andykarpov/PiRadio-20x4LCD/schematic/build/pdf/volume_v_1_0_pcb_top.pdf

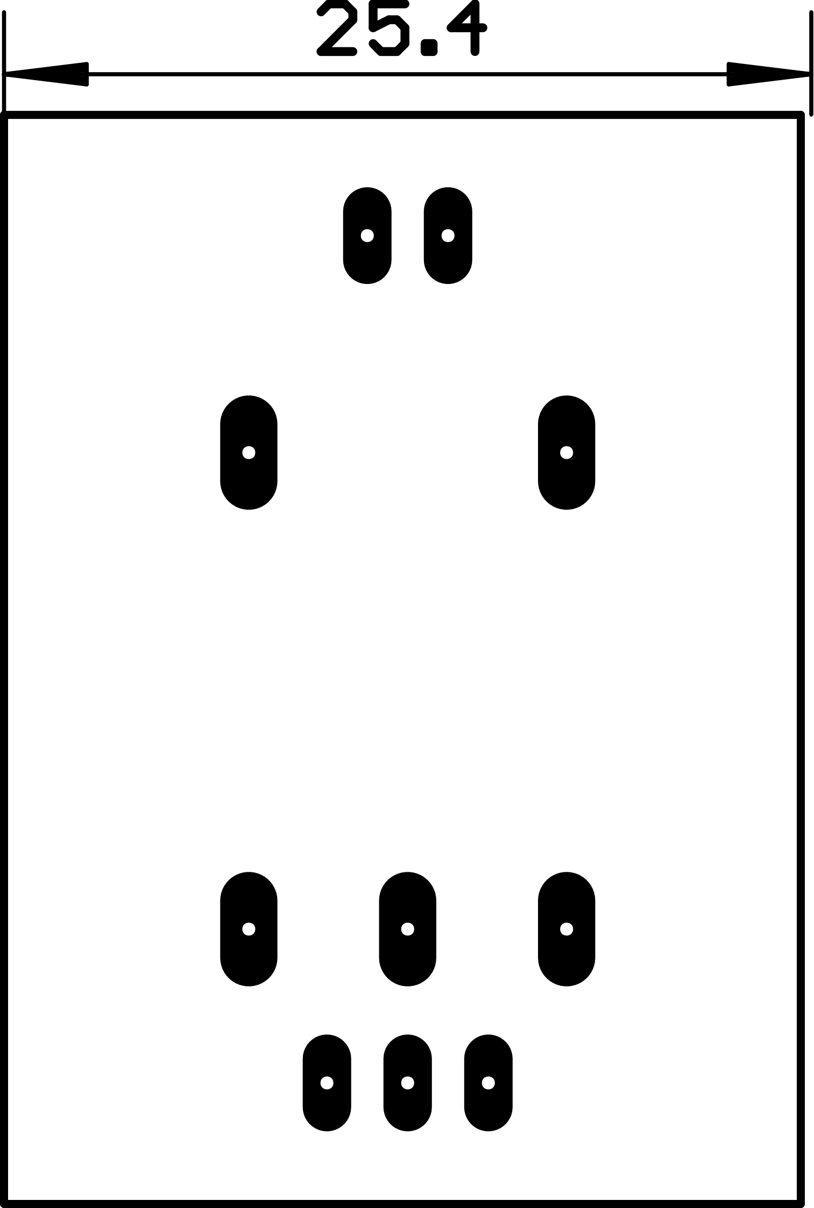
[picture p1: figure]
