andykarpov/PiRadio-20x4LCD/schematic/build/png/encoder_v_1_0_pcb_top.png

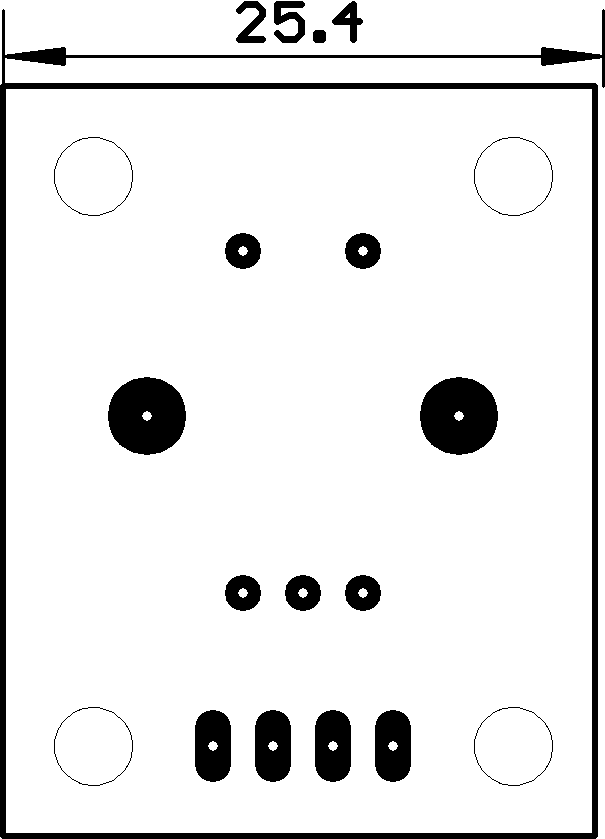
schematic/build/png/encoder_v_1_0_pcb_top.png
