andykarpov/PiRadio-20x4LCD/schematic/build/png/interface_v_1_0_pcb_bottom_vertical.png

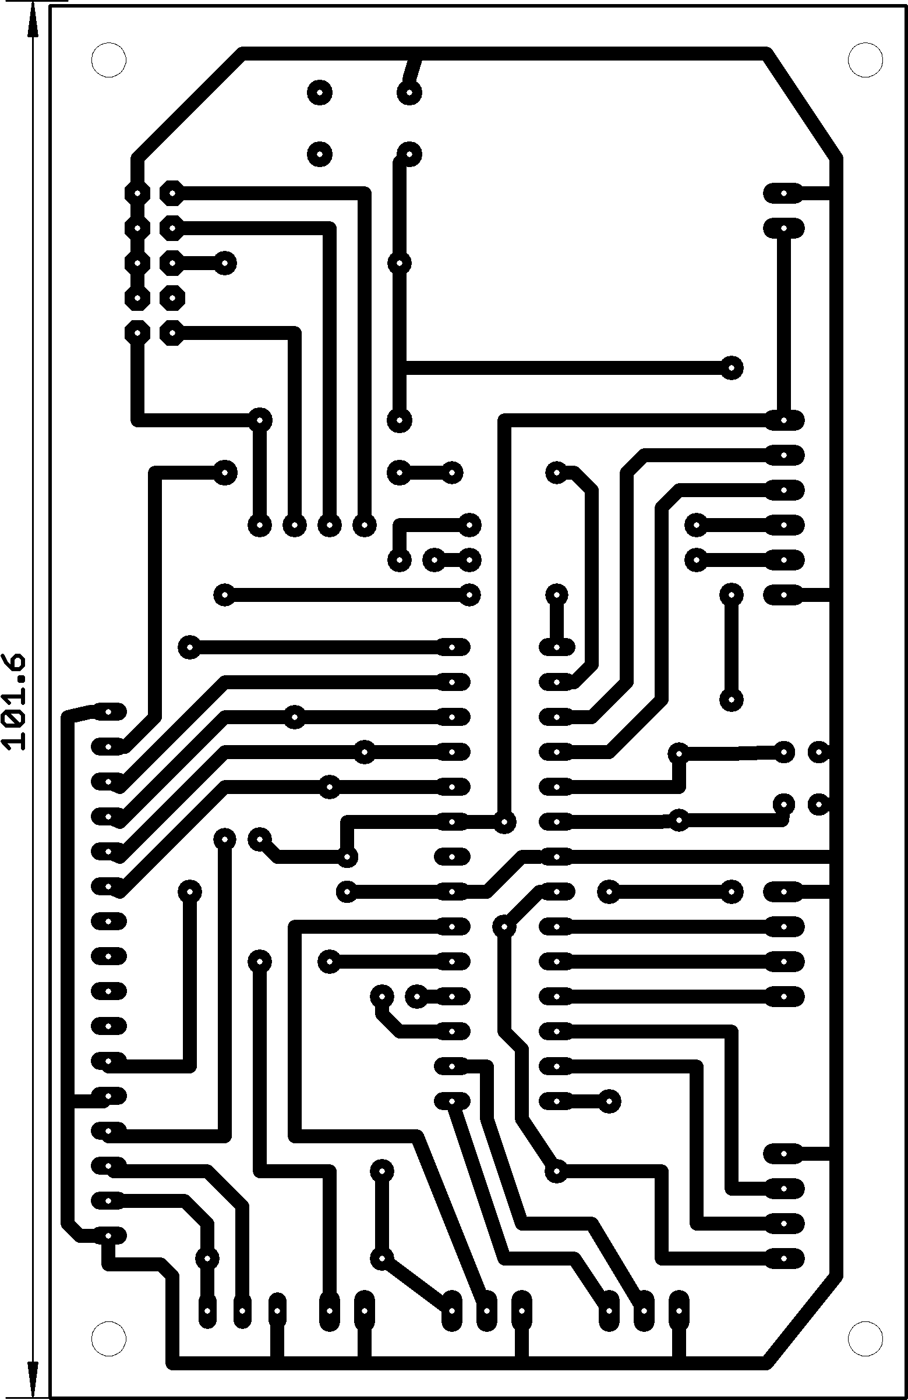
schematic/build/png/interface_v_1_0_pcb_bottom_vertical.png
