andykarpov/PiRadio-20x4LCD/schematic/build/png/pt2322_v_1_0_pcb_top_mirror.png

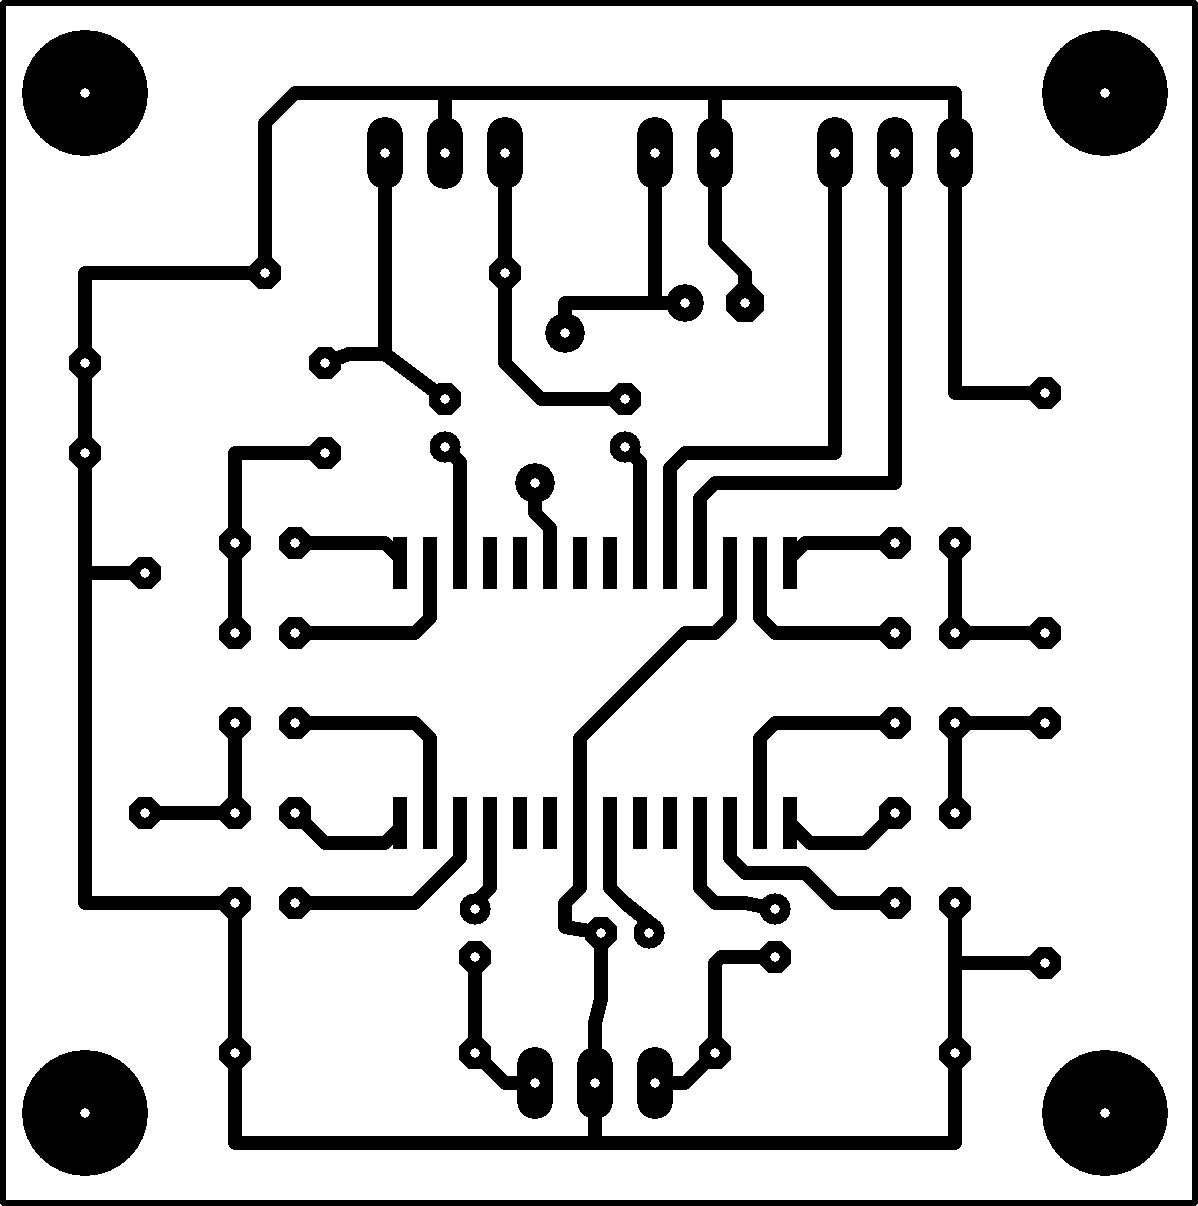
schematic/build/png/pt2322_v_1_0_pcb_top_mirror.png
