andykarpov/PiRadio-20x4LCD/schematic/build/png/tda8425_v_1_0_pcb_cmp_jumpered.png

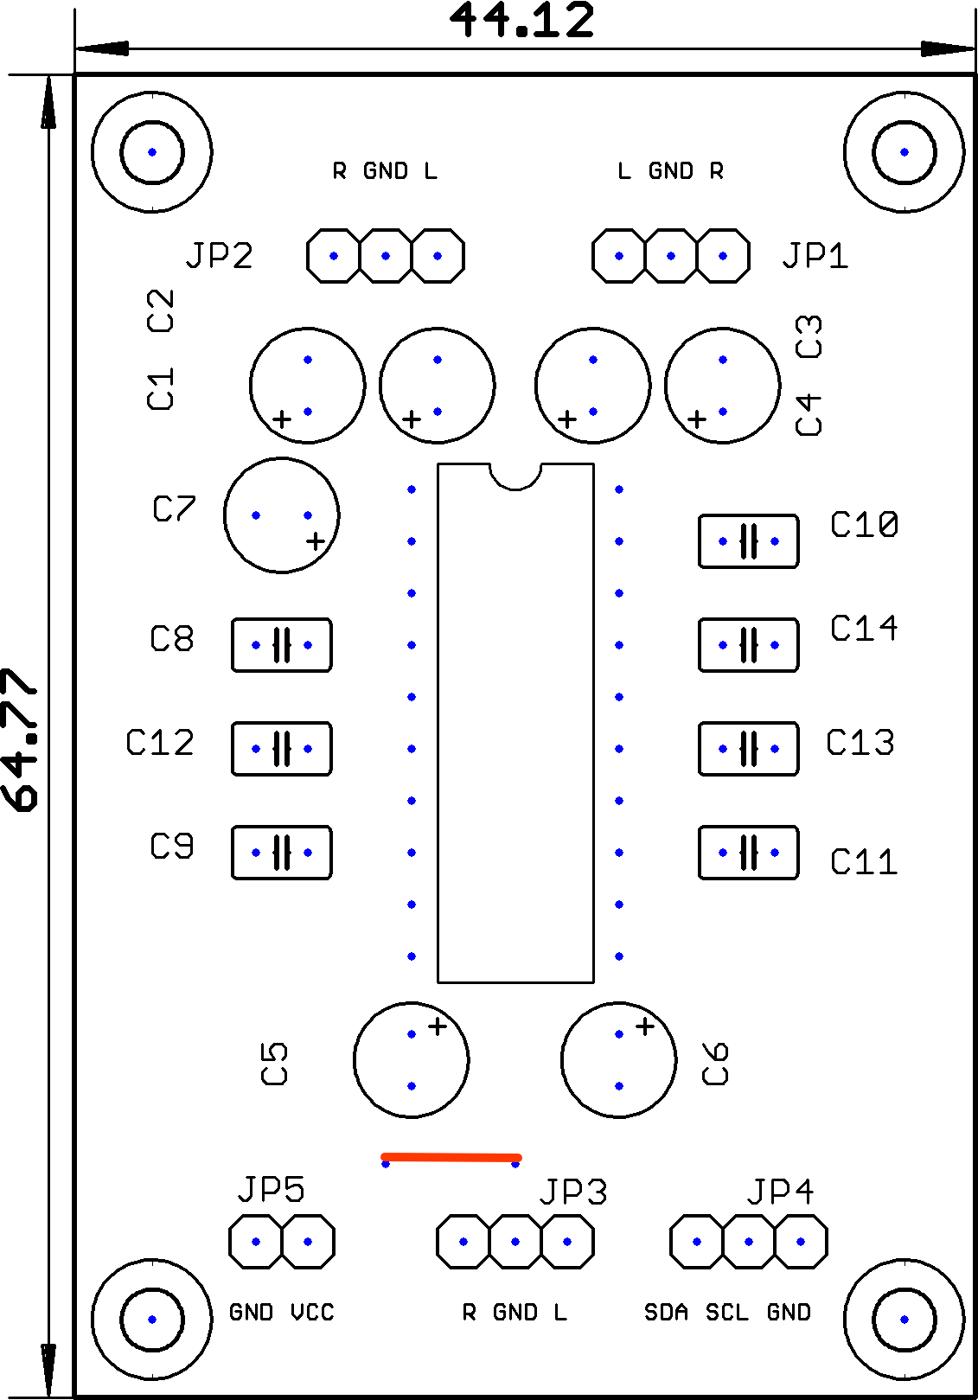
schematic/build/png/tda8425_v_1_0_pcb_cmp_jumpered.png
