andykarpov/PiRadio-20x4LCD/schematic/build/png/test_v_1_0_pcb_cmp.png

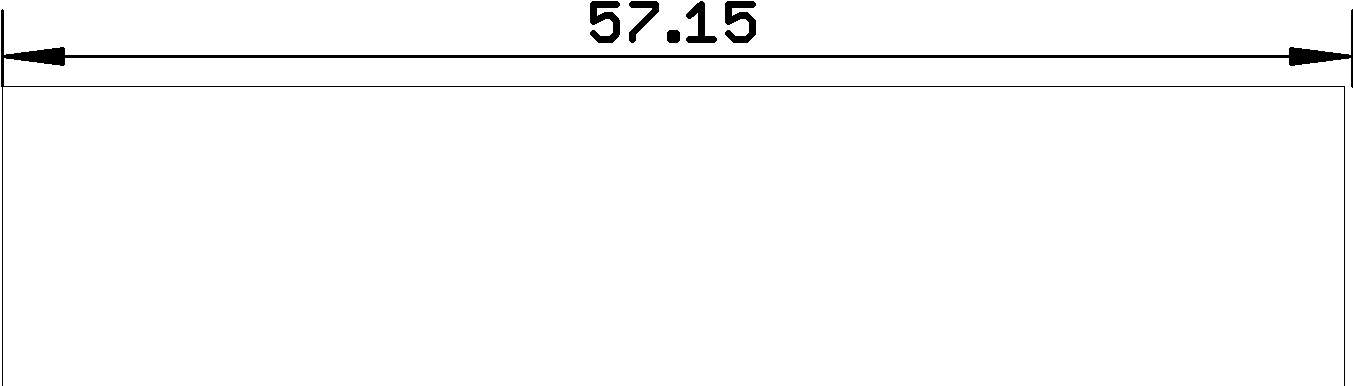
schematic/build/png/test_v_1_0_pcb_cmp.png
