andykarpov/PiRadio-20x4LCD/schematic/build/pdf/encoder_v_1_0_pcb_bottom.pdf

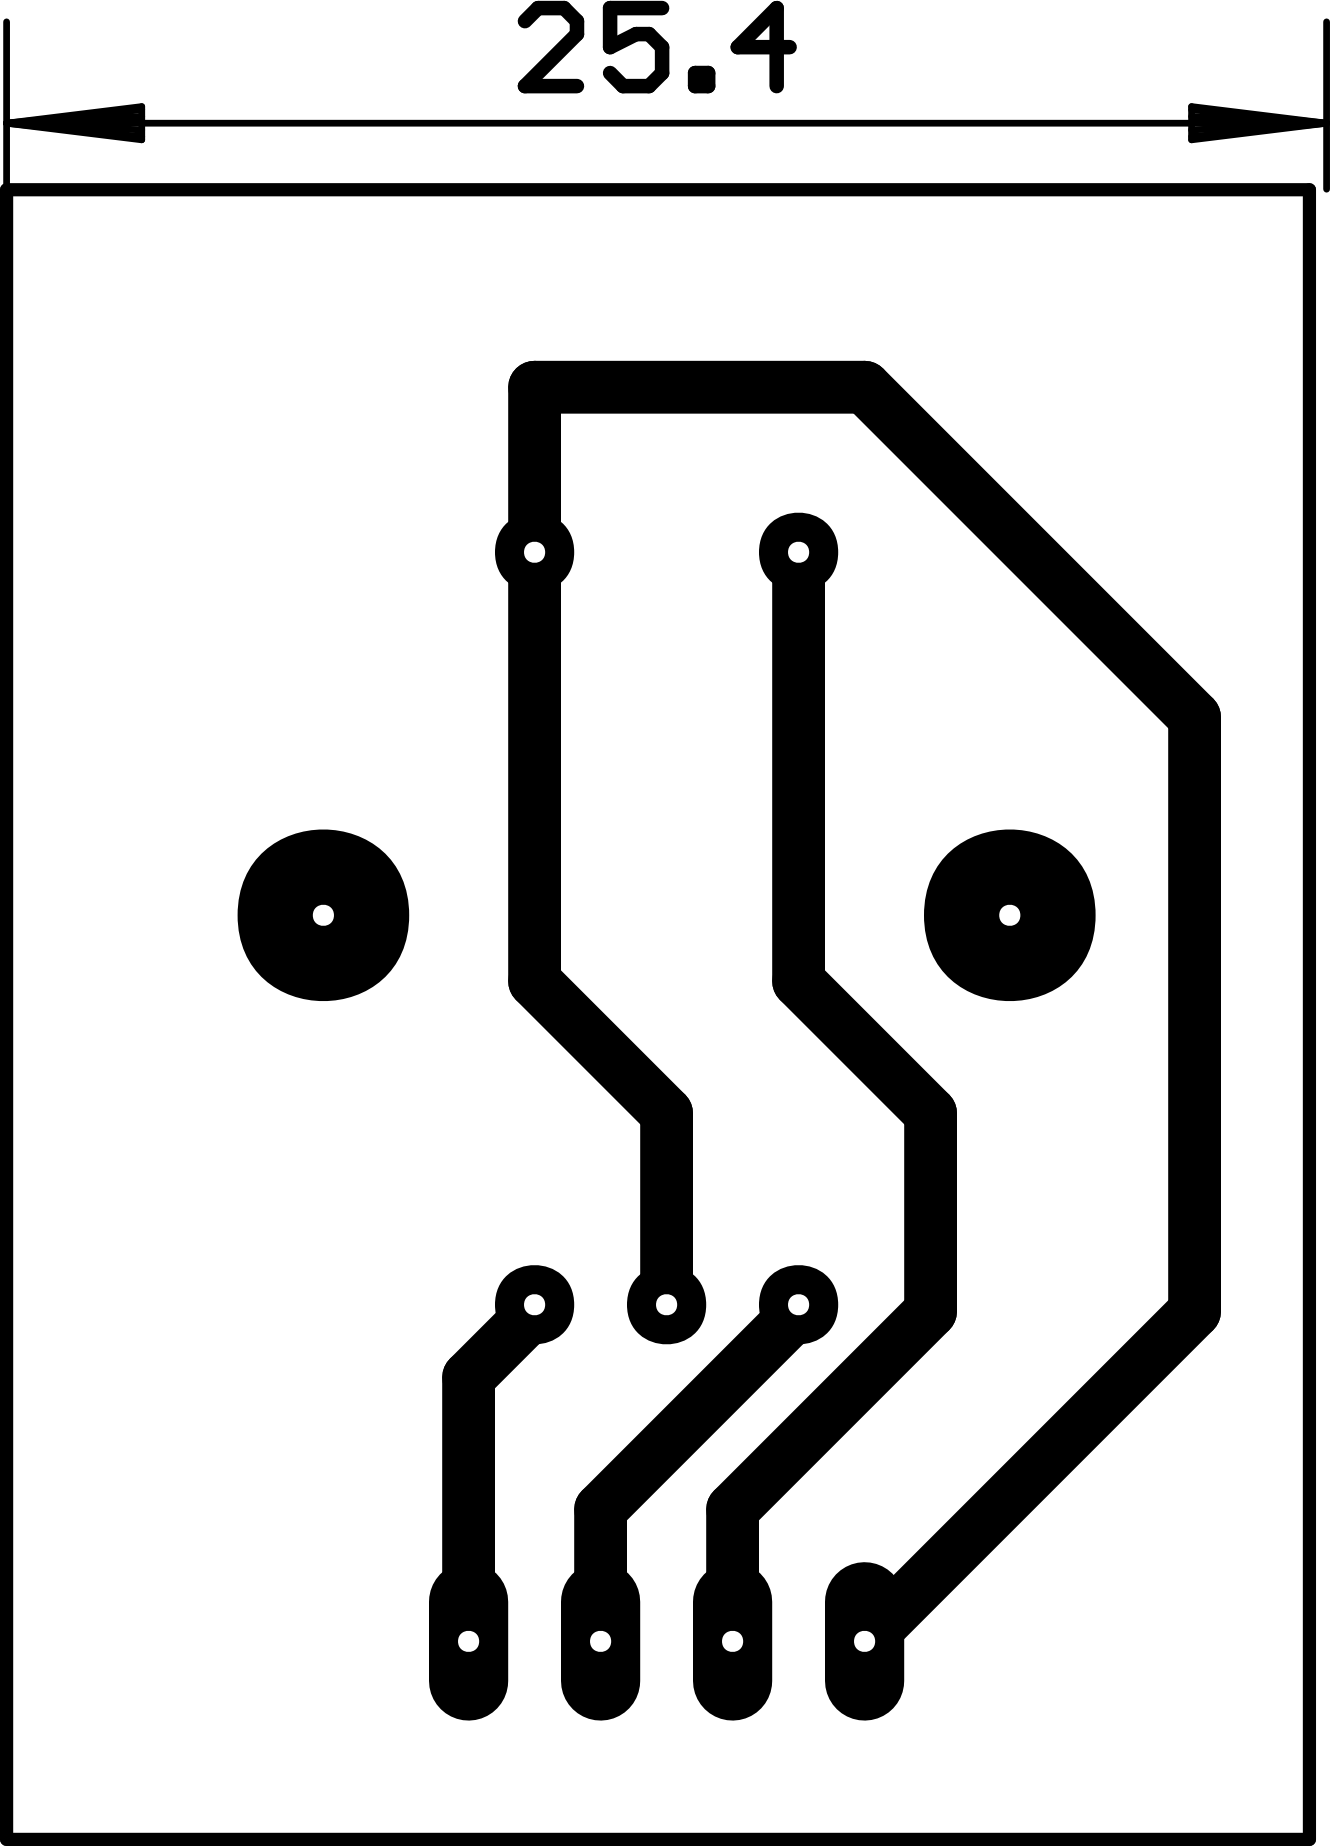
[picture p18: page 1]
