andykarpov/PiRadio-20x4LCD/schematic/build/pdf/encoder_v_1_0_pcb_cmp.pdf

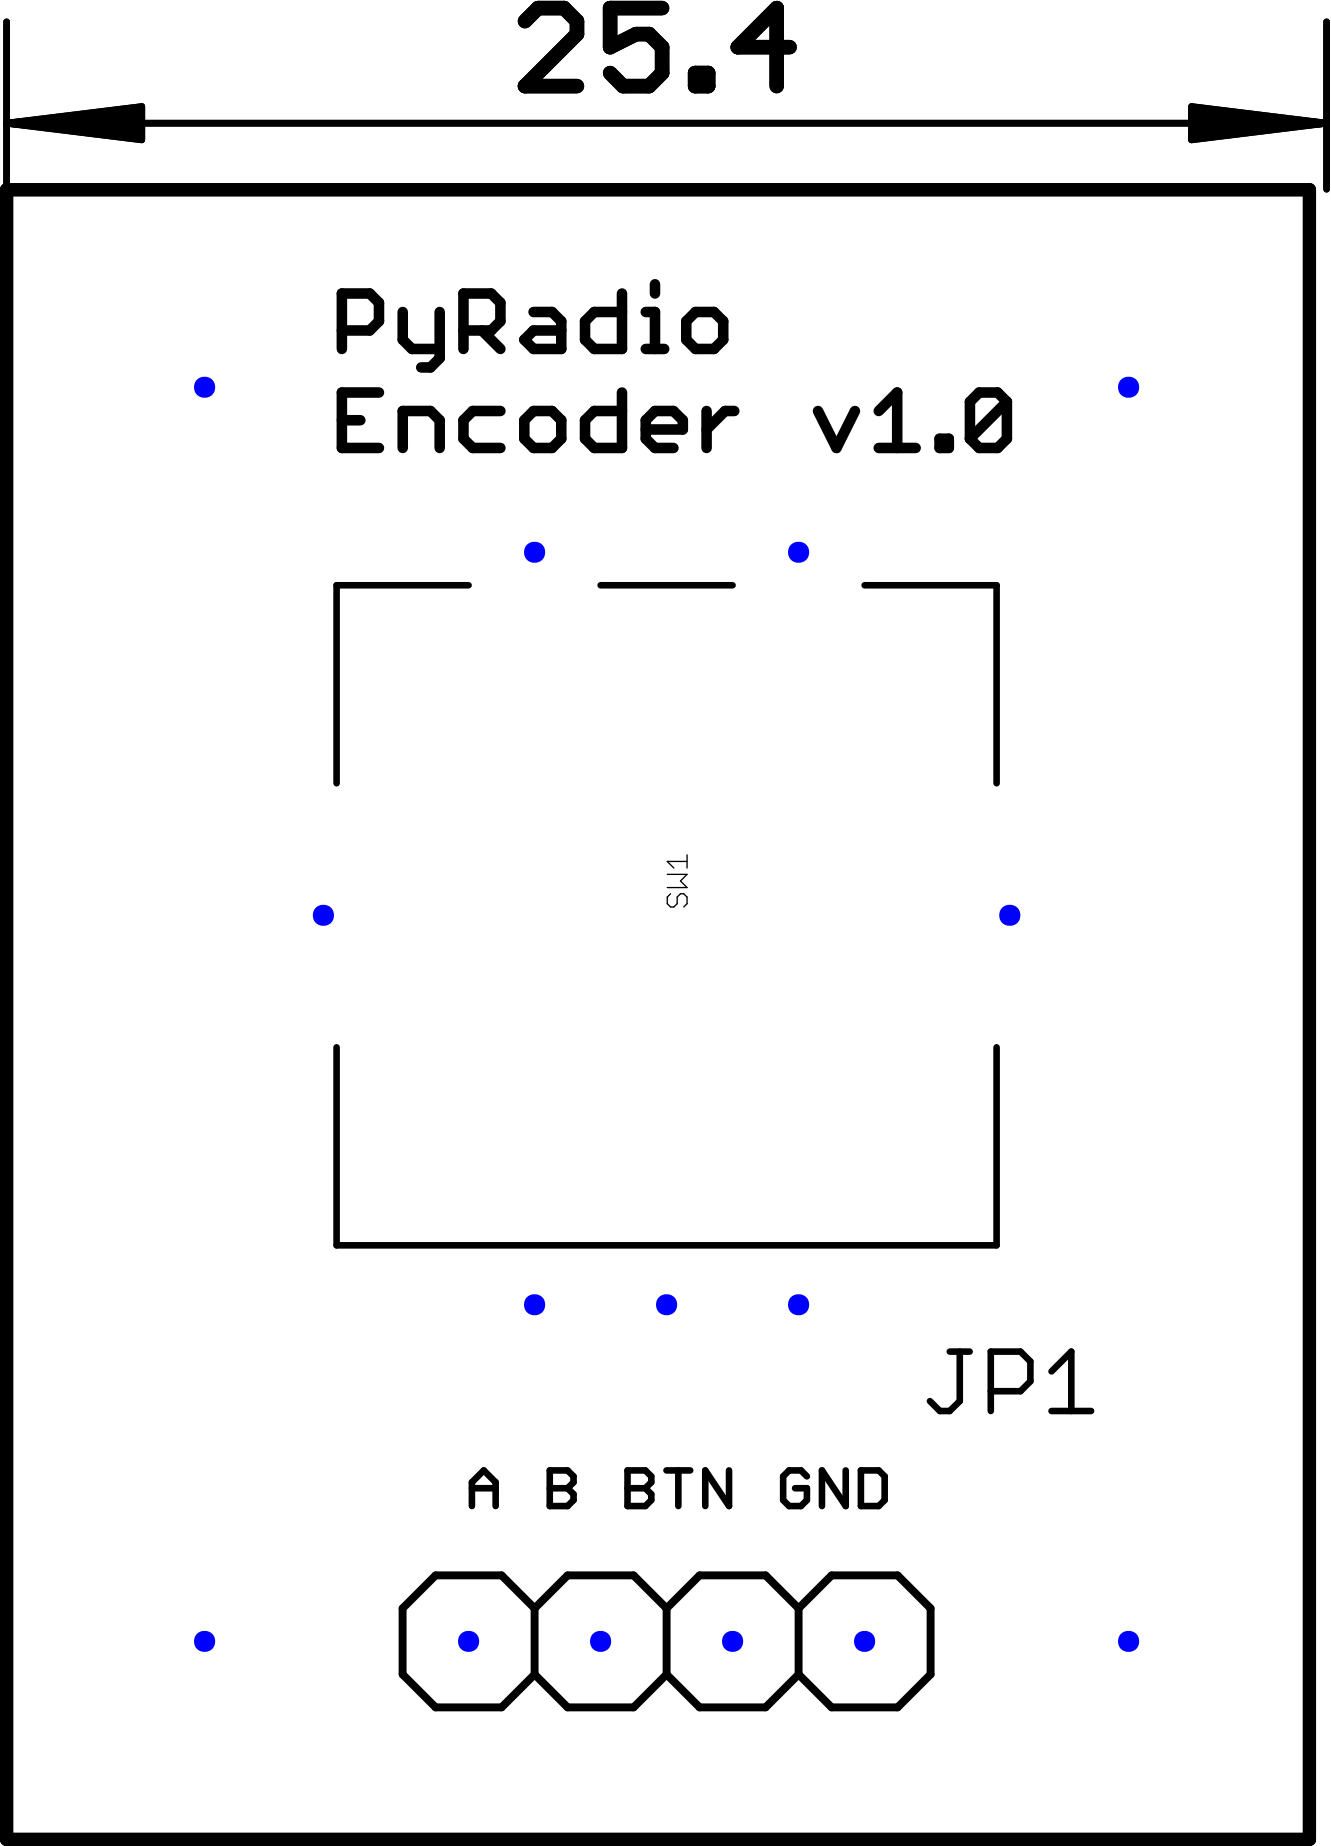
[picture p19: page 1]
