andykarpov/PiRadio-20x4LCD/schematic/build/pdf/encoder_v_1_0_pcb_top.pdf

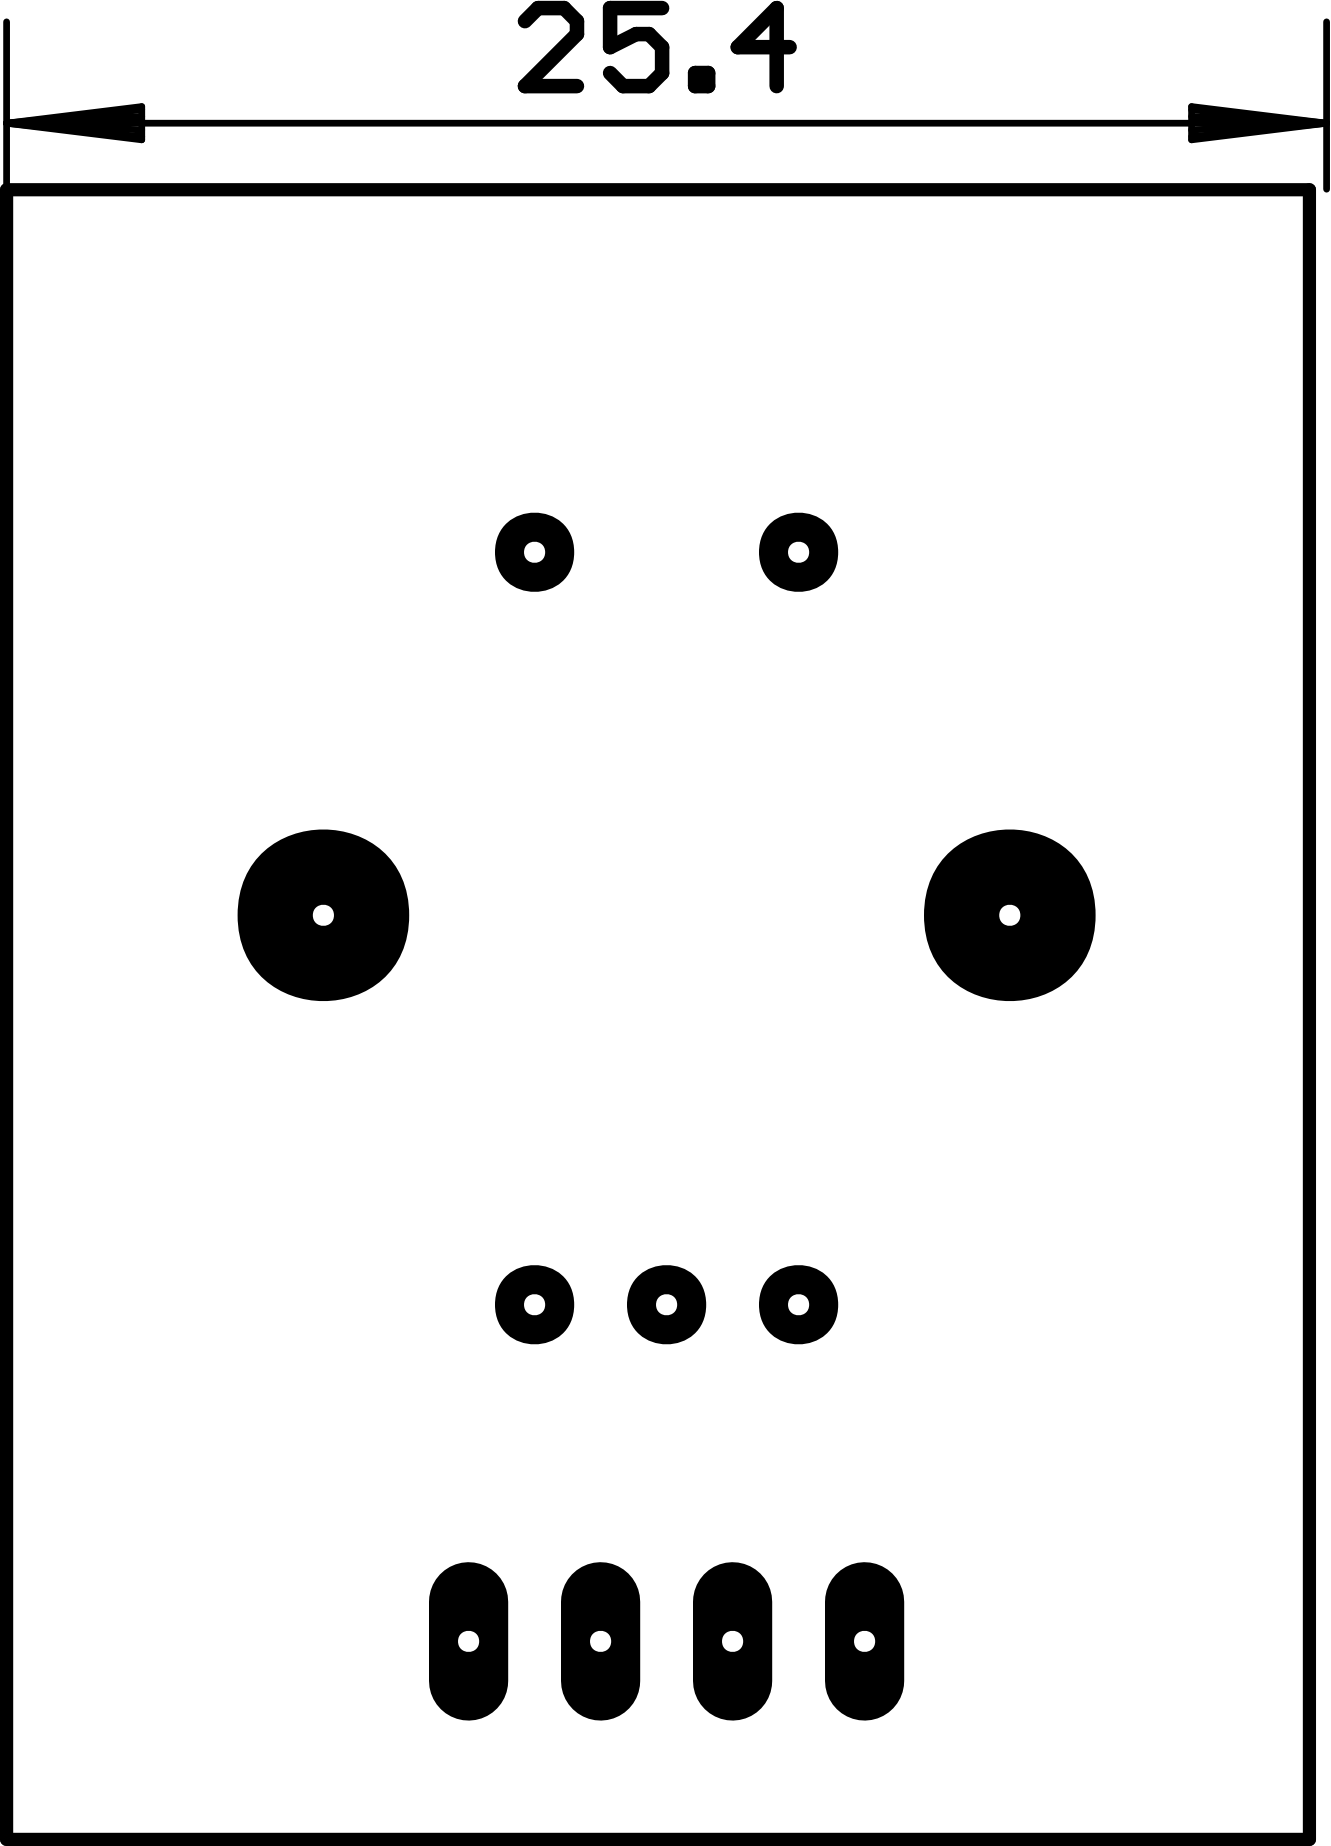
[picture p20: page 1]
