andykarpov/PiRadio-20x4LCD/schematic/build/pdf/interface_v_1_0_pcb_bottom.pdf

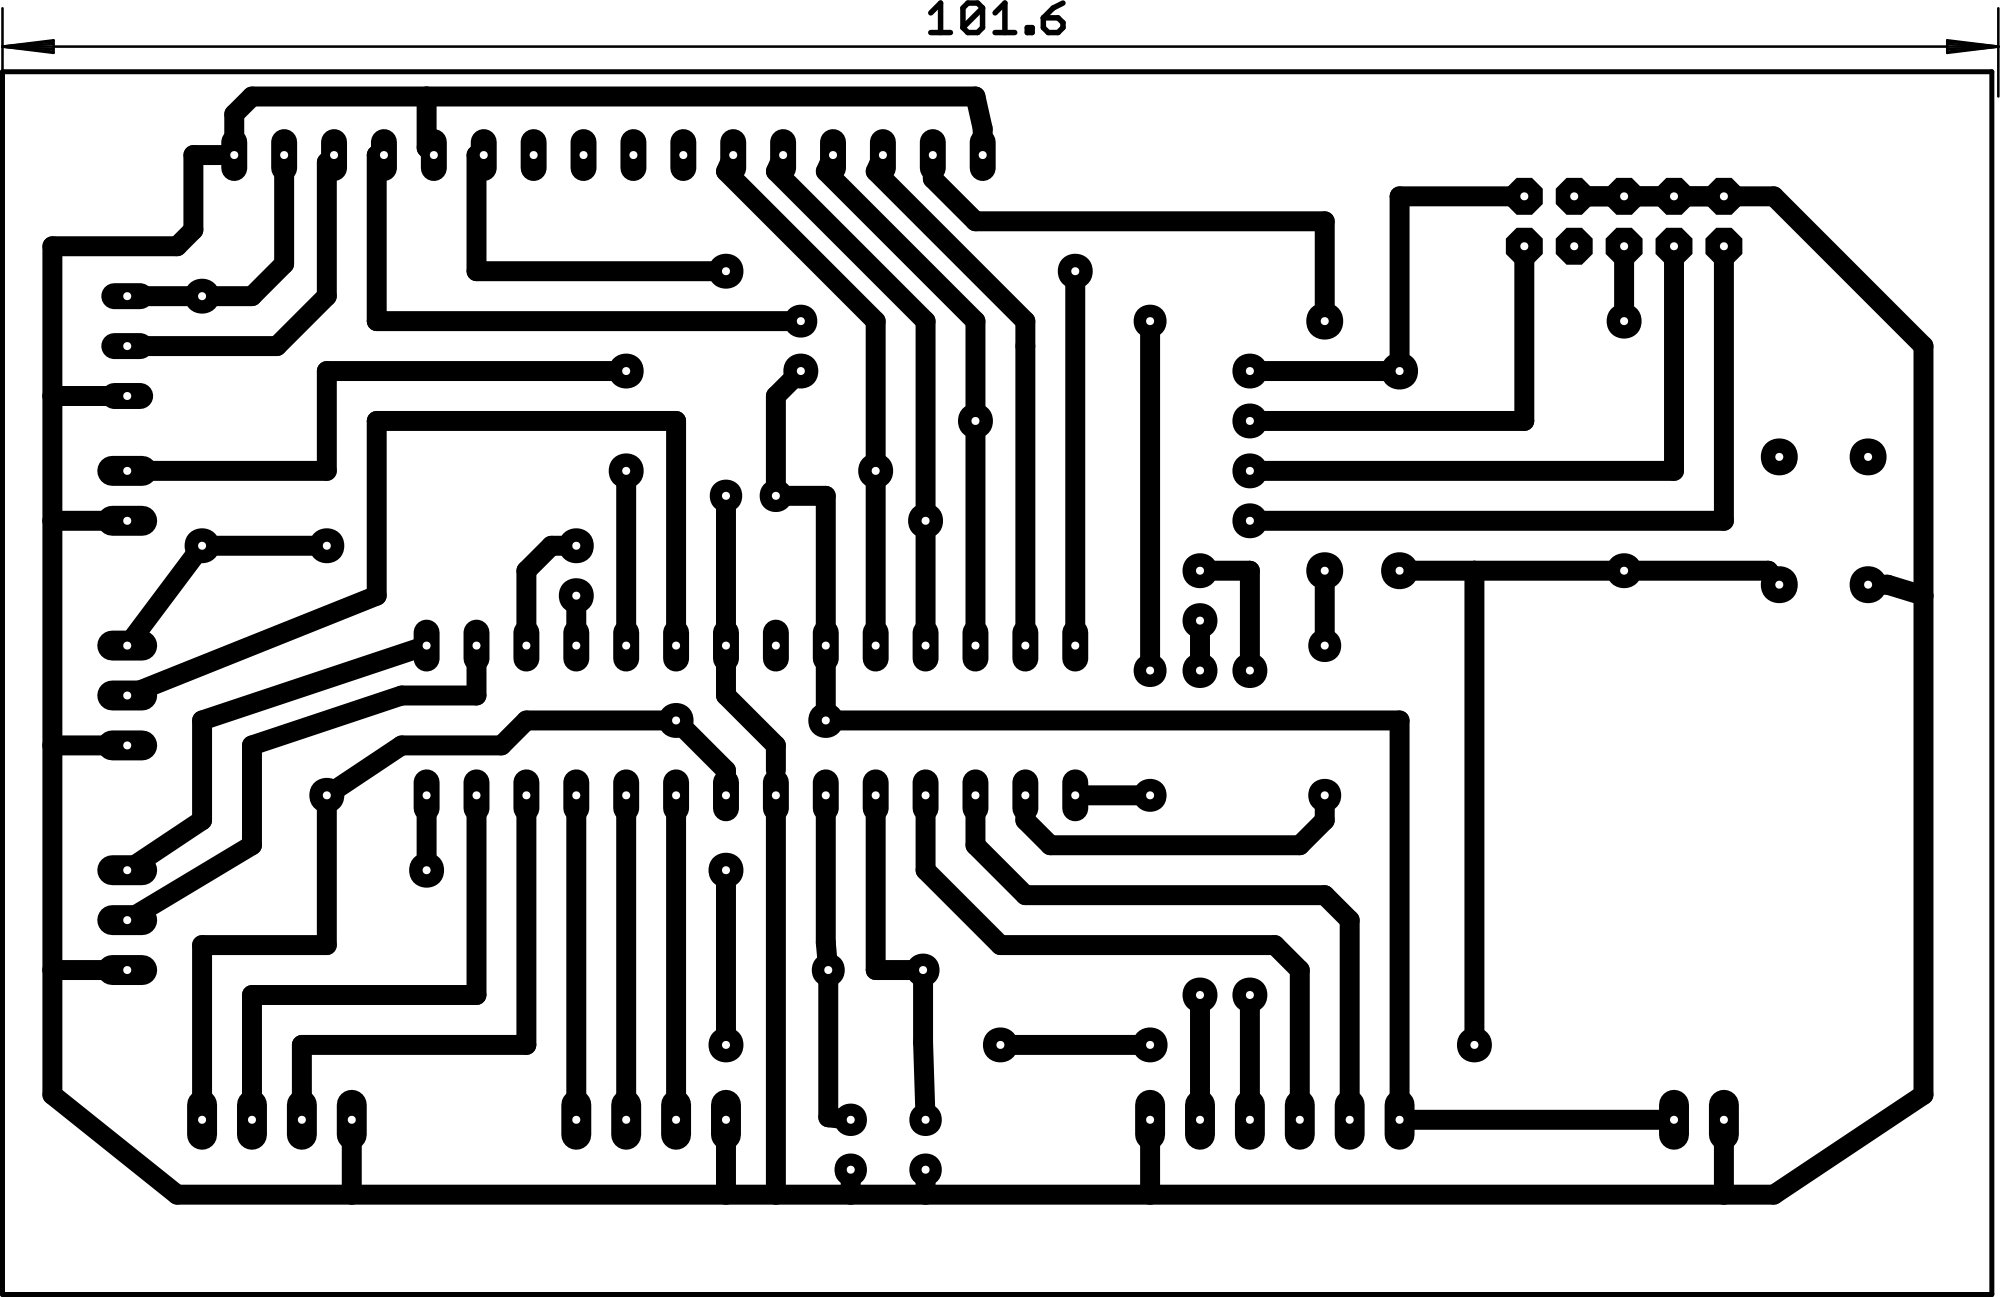
[picture p21: page 1]
