andykarpov/PiRadio-20x4LCD/schematic/build/pdf/interface_v_1_0_pcb_cmp.pdf

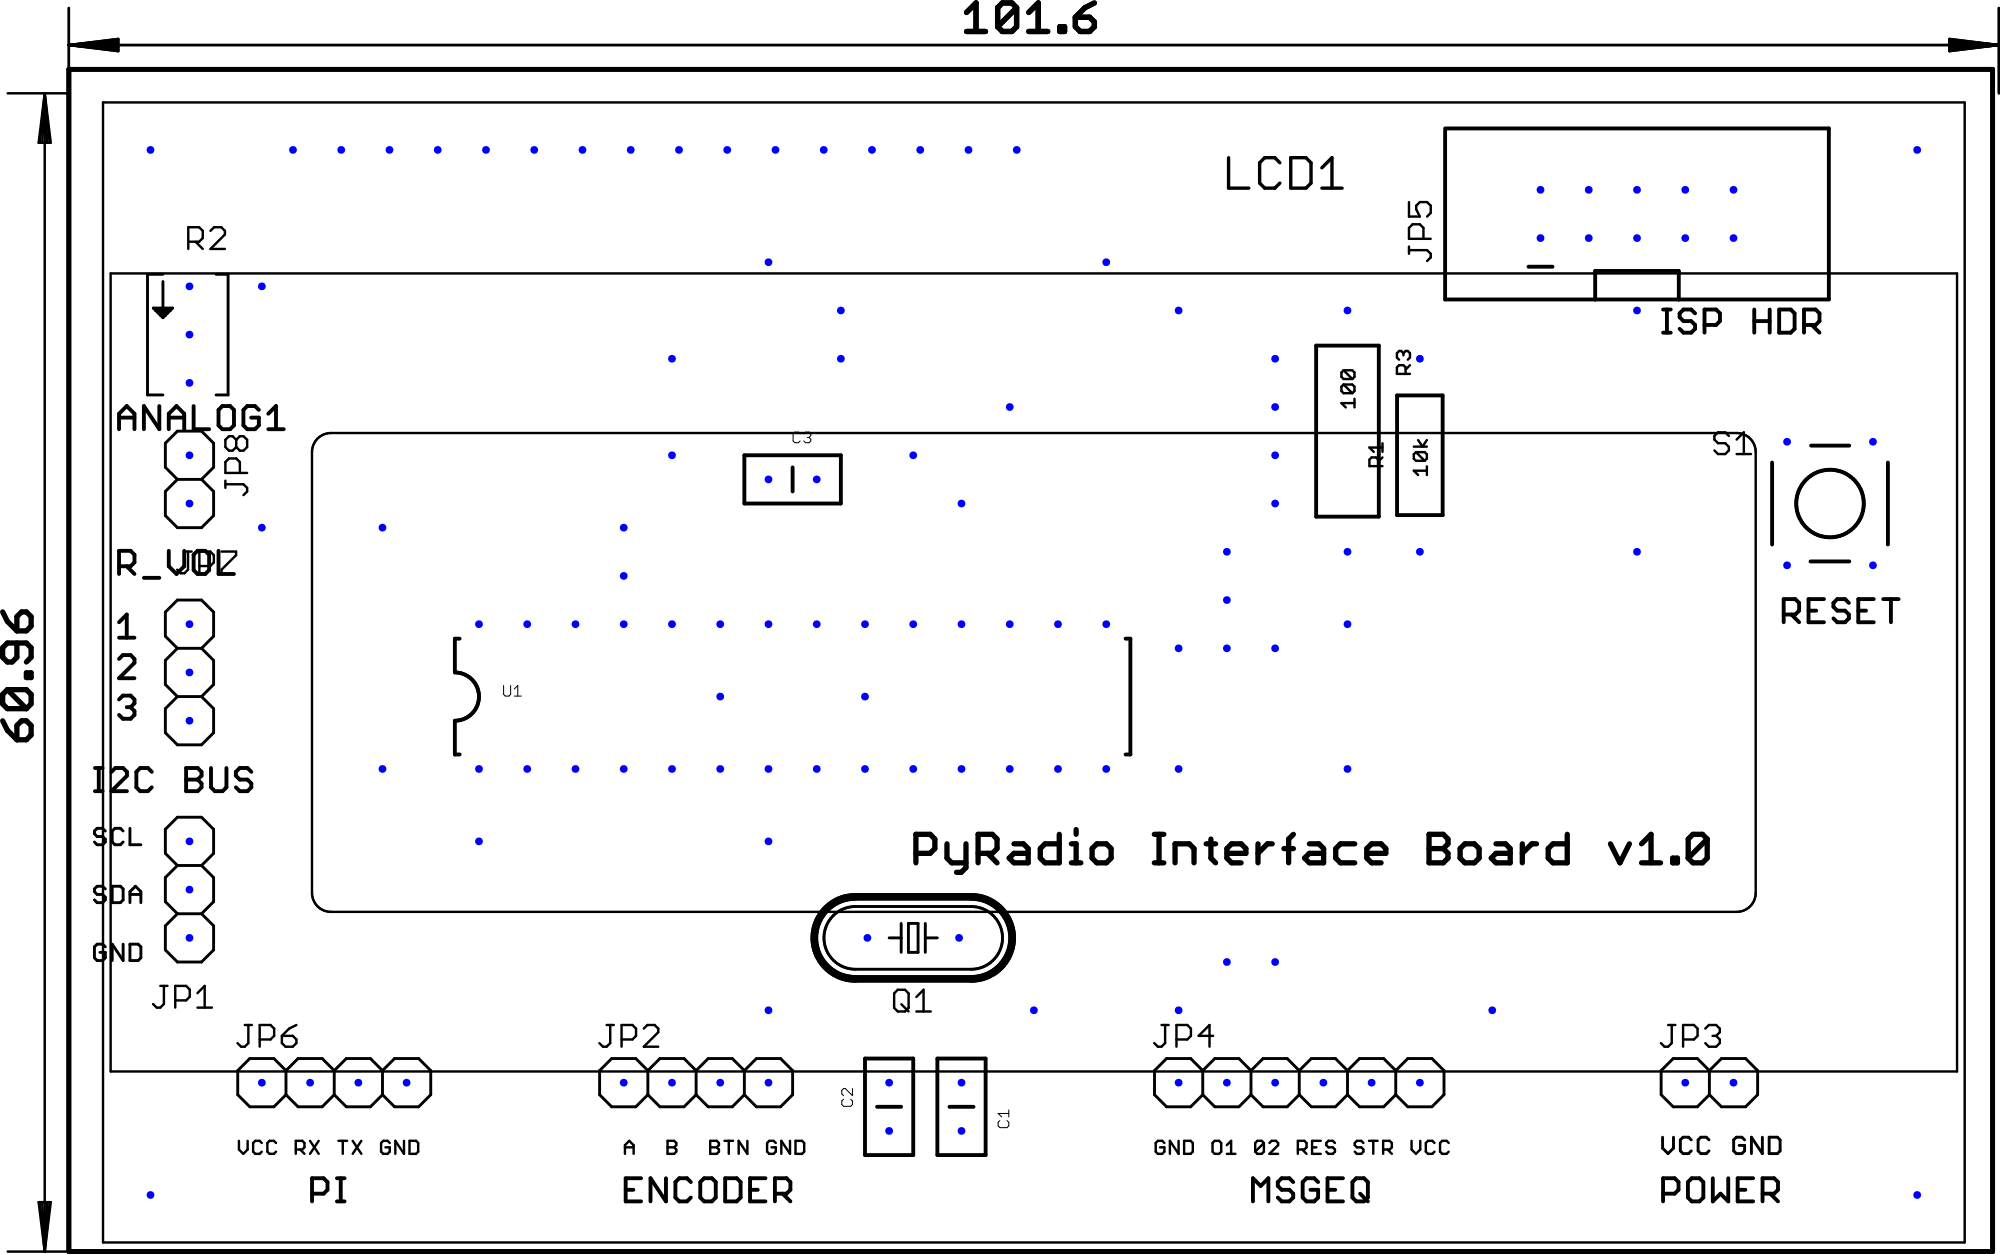
[picture p22: page 1]
