andykarpov/PiRadio-20x4LCD/schematic/build/pdf/interface_v_1_0_pcb_top.pdf

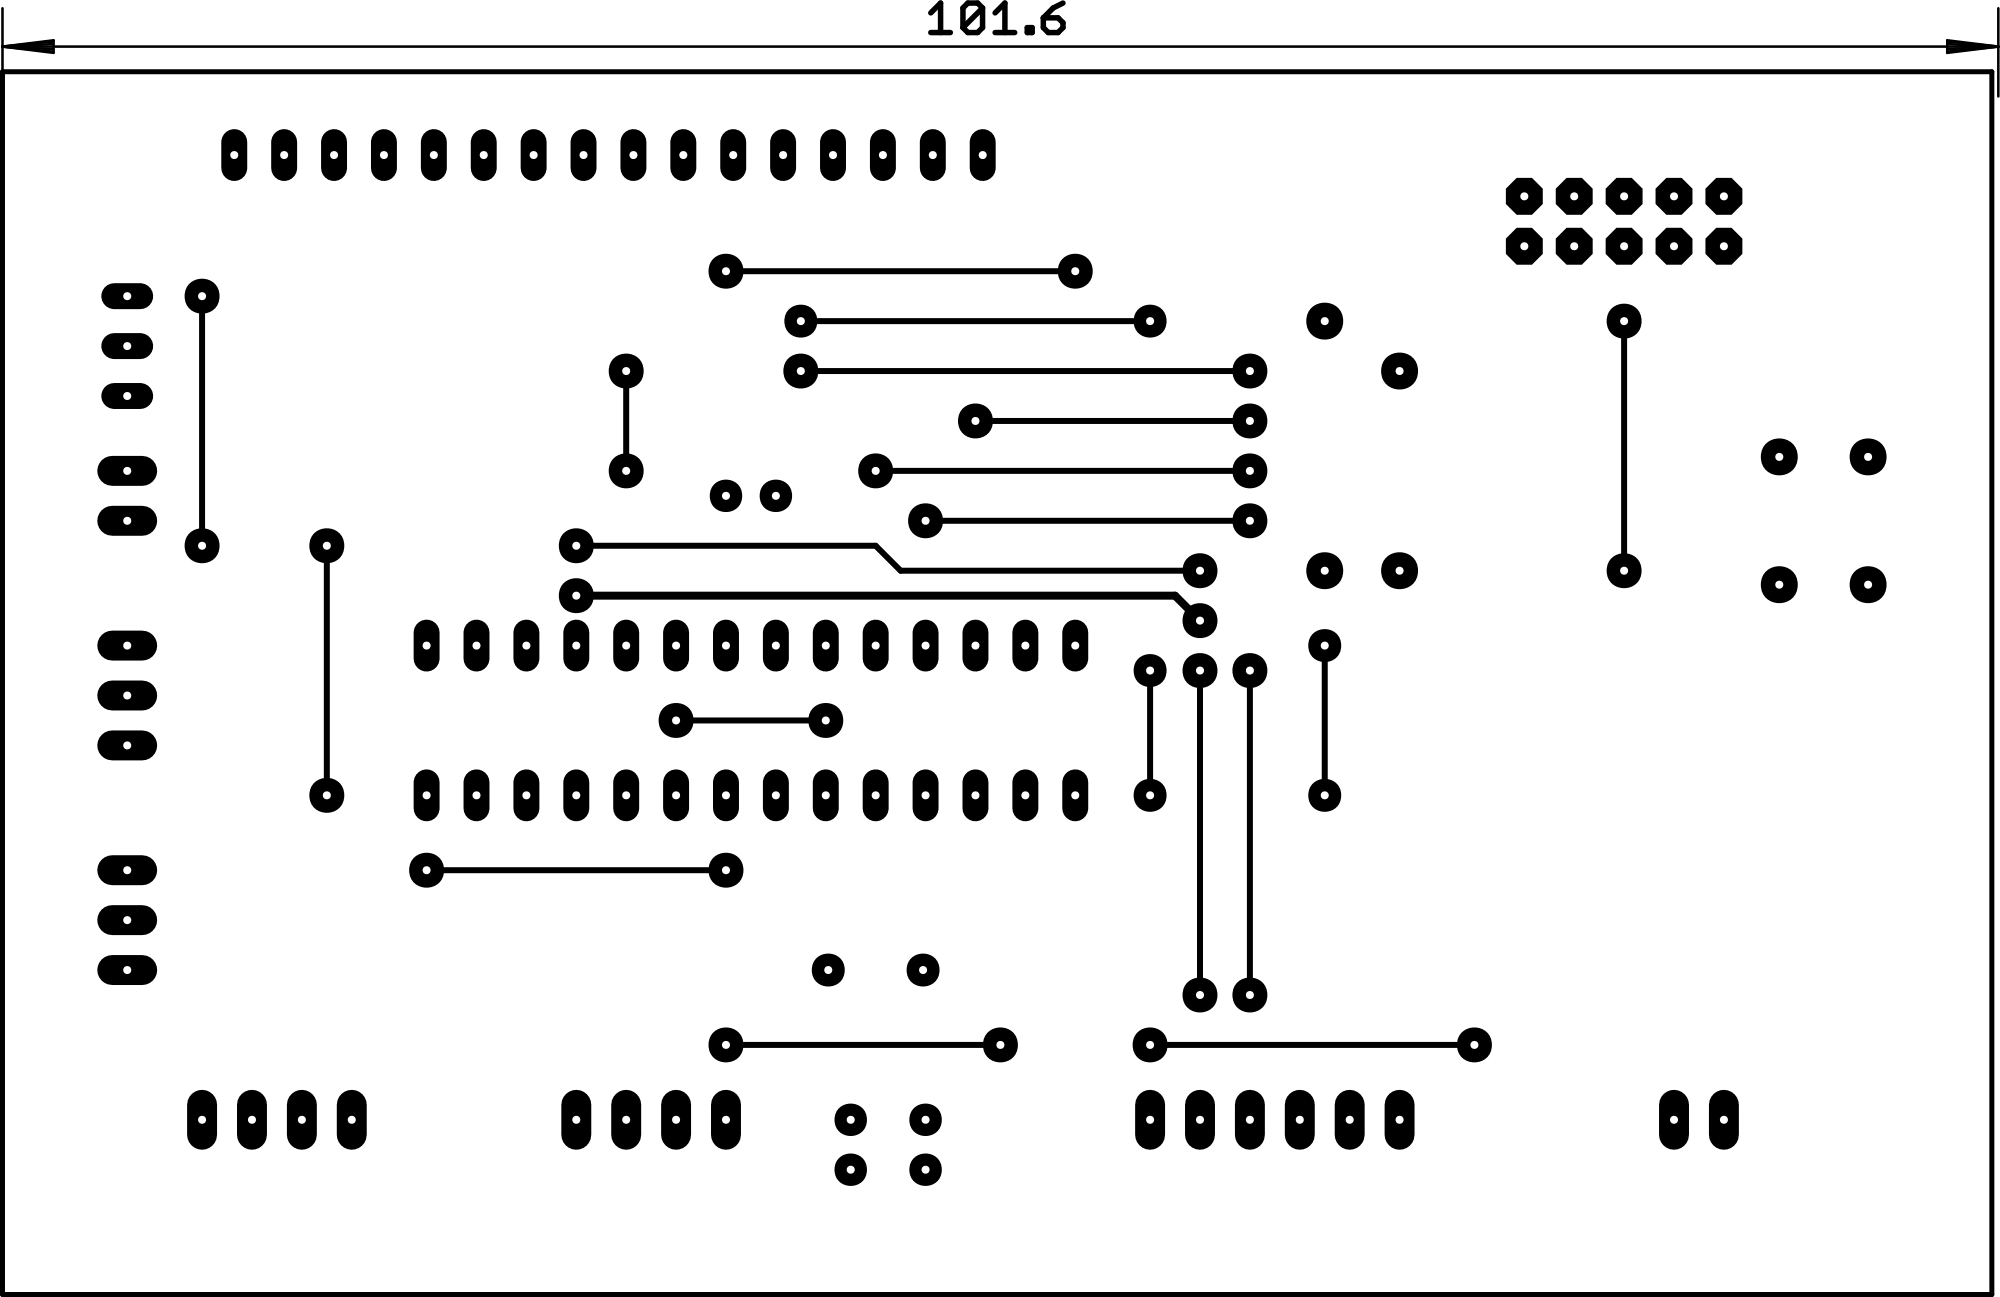
[picture p23: page 1]
