andykarpov/PiRadio-20x4LCD/schematic/build/pdf/msgeq7_v_1_0_pcb_bottom.pdf

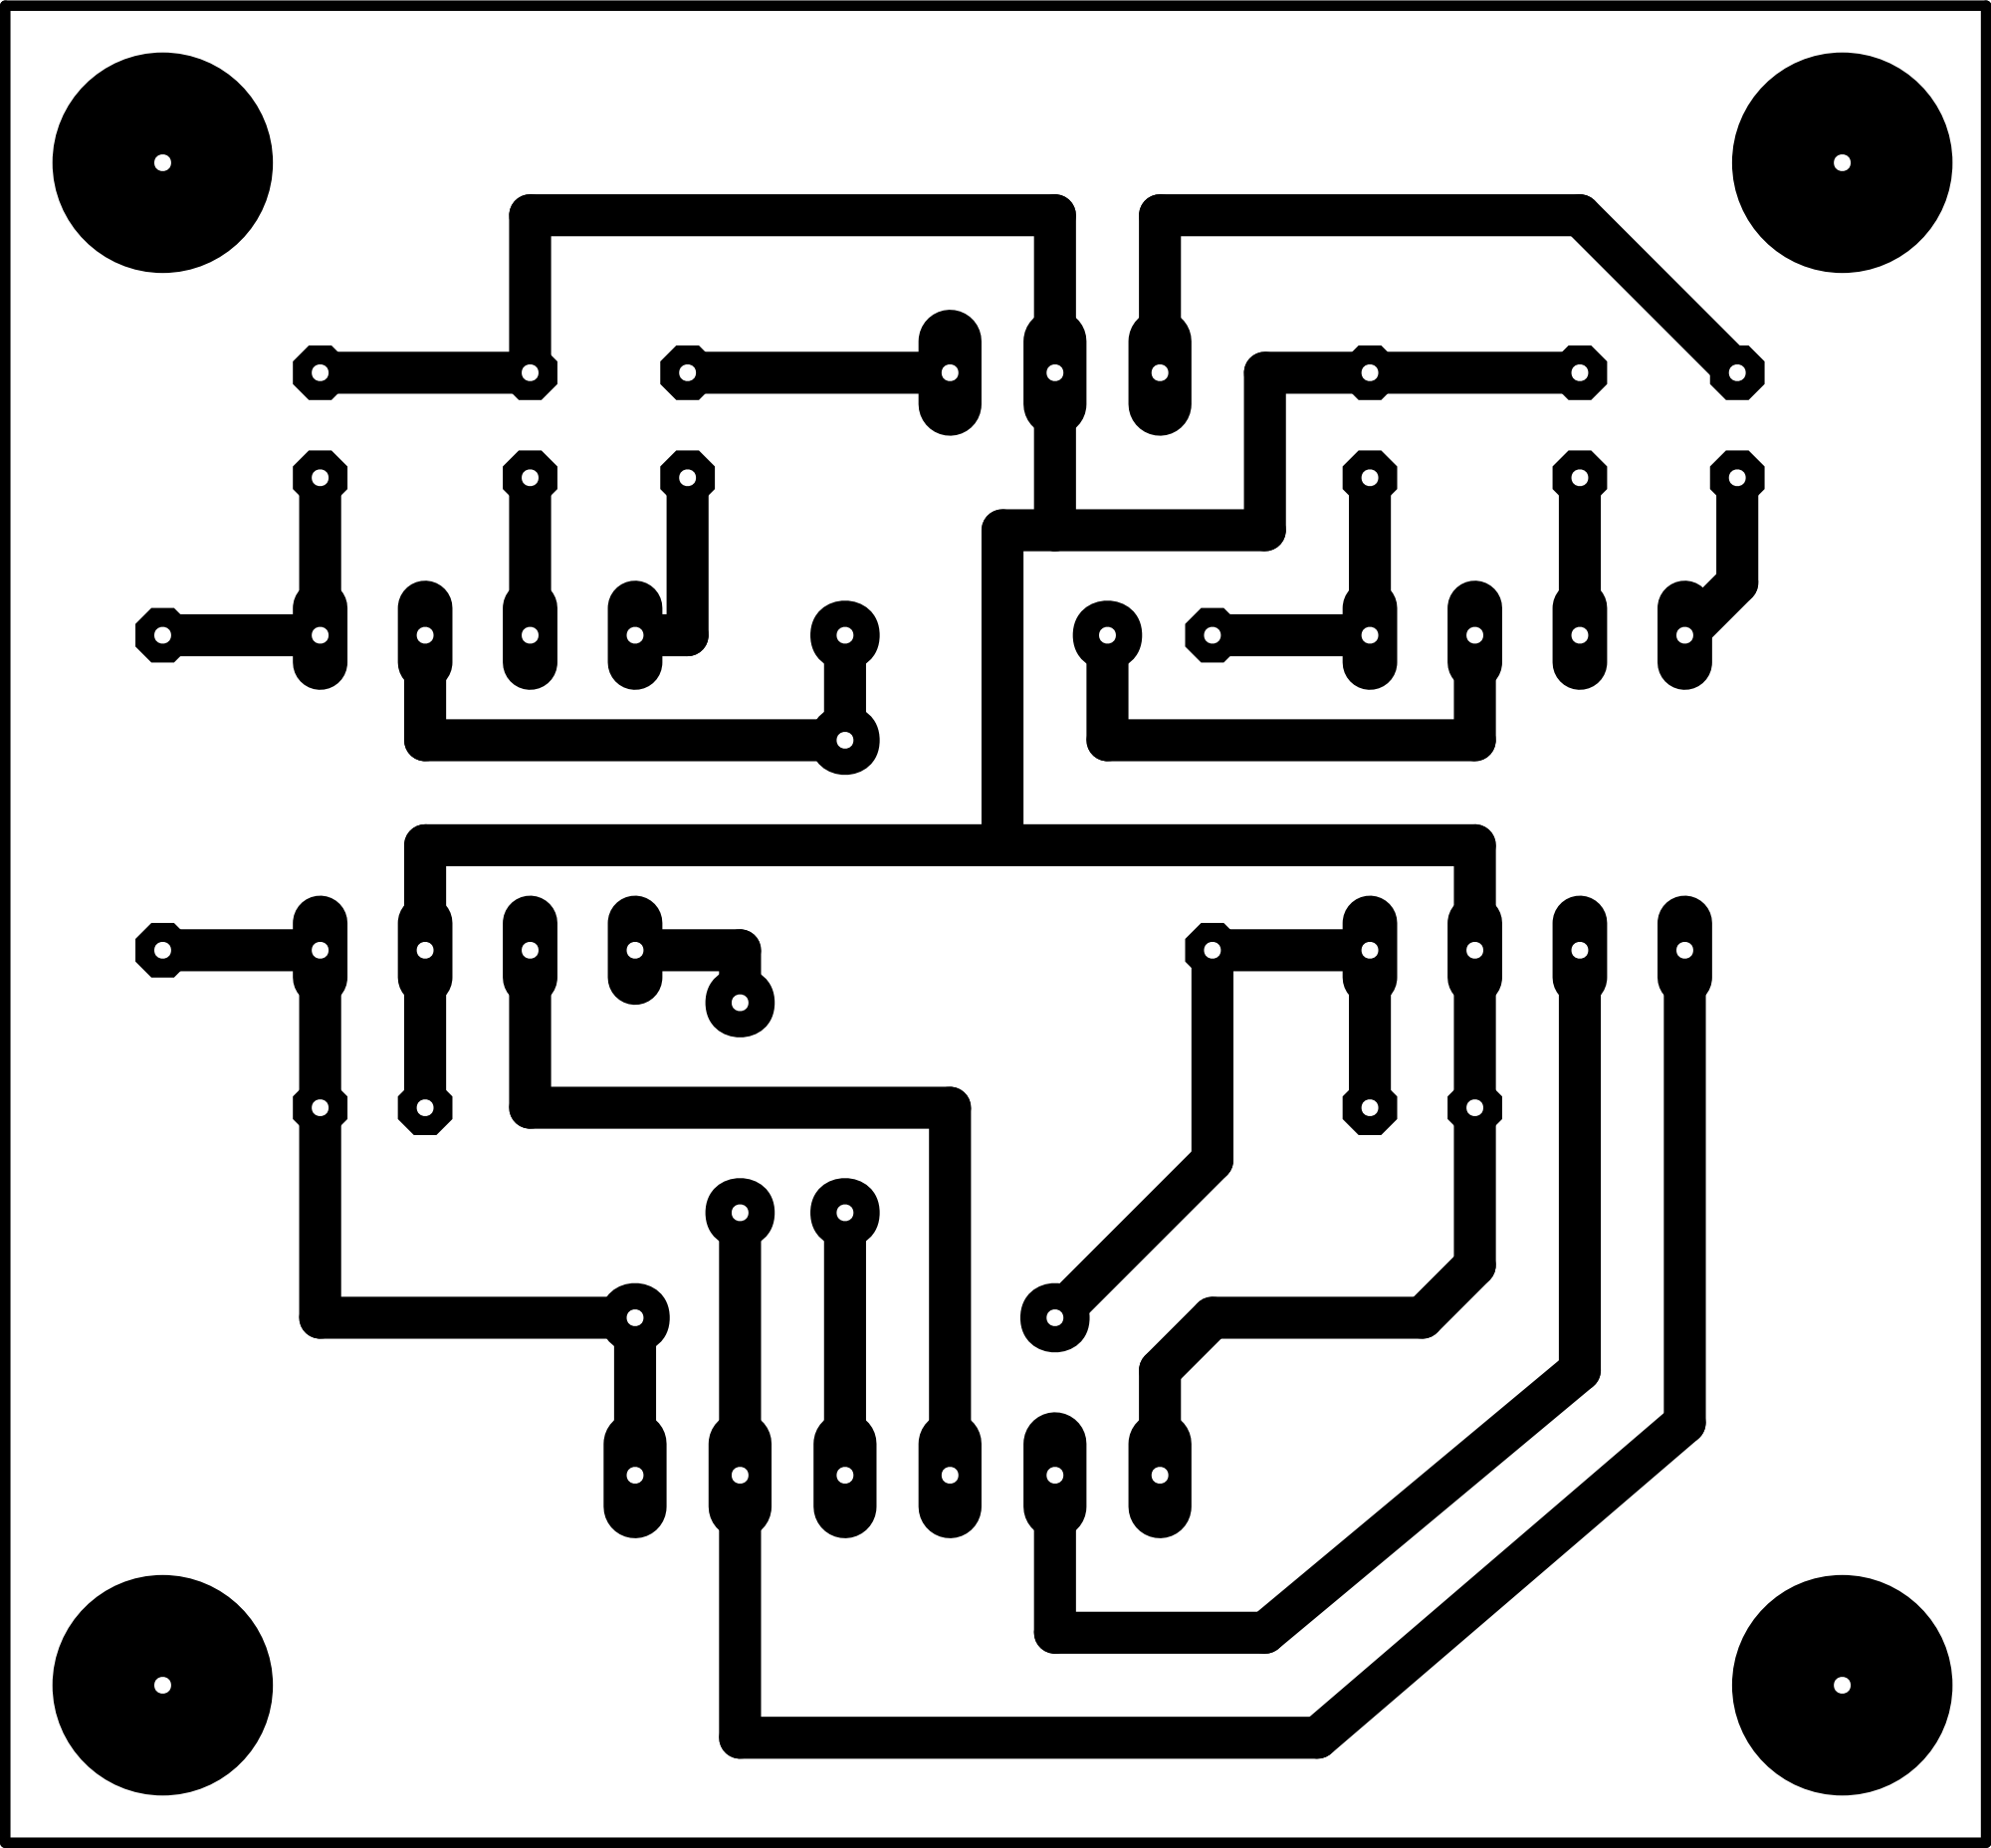
[picture p24: page 1]
