andykarpov/PiRadio-20x4LCD/schematic/build/pdf/msgeq7_v_1_0_pcb_cmp.pdf

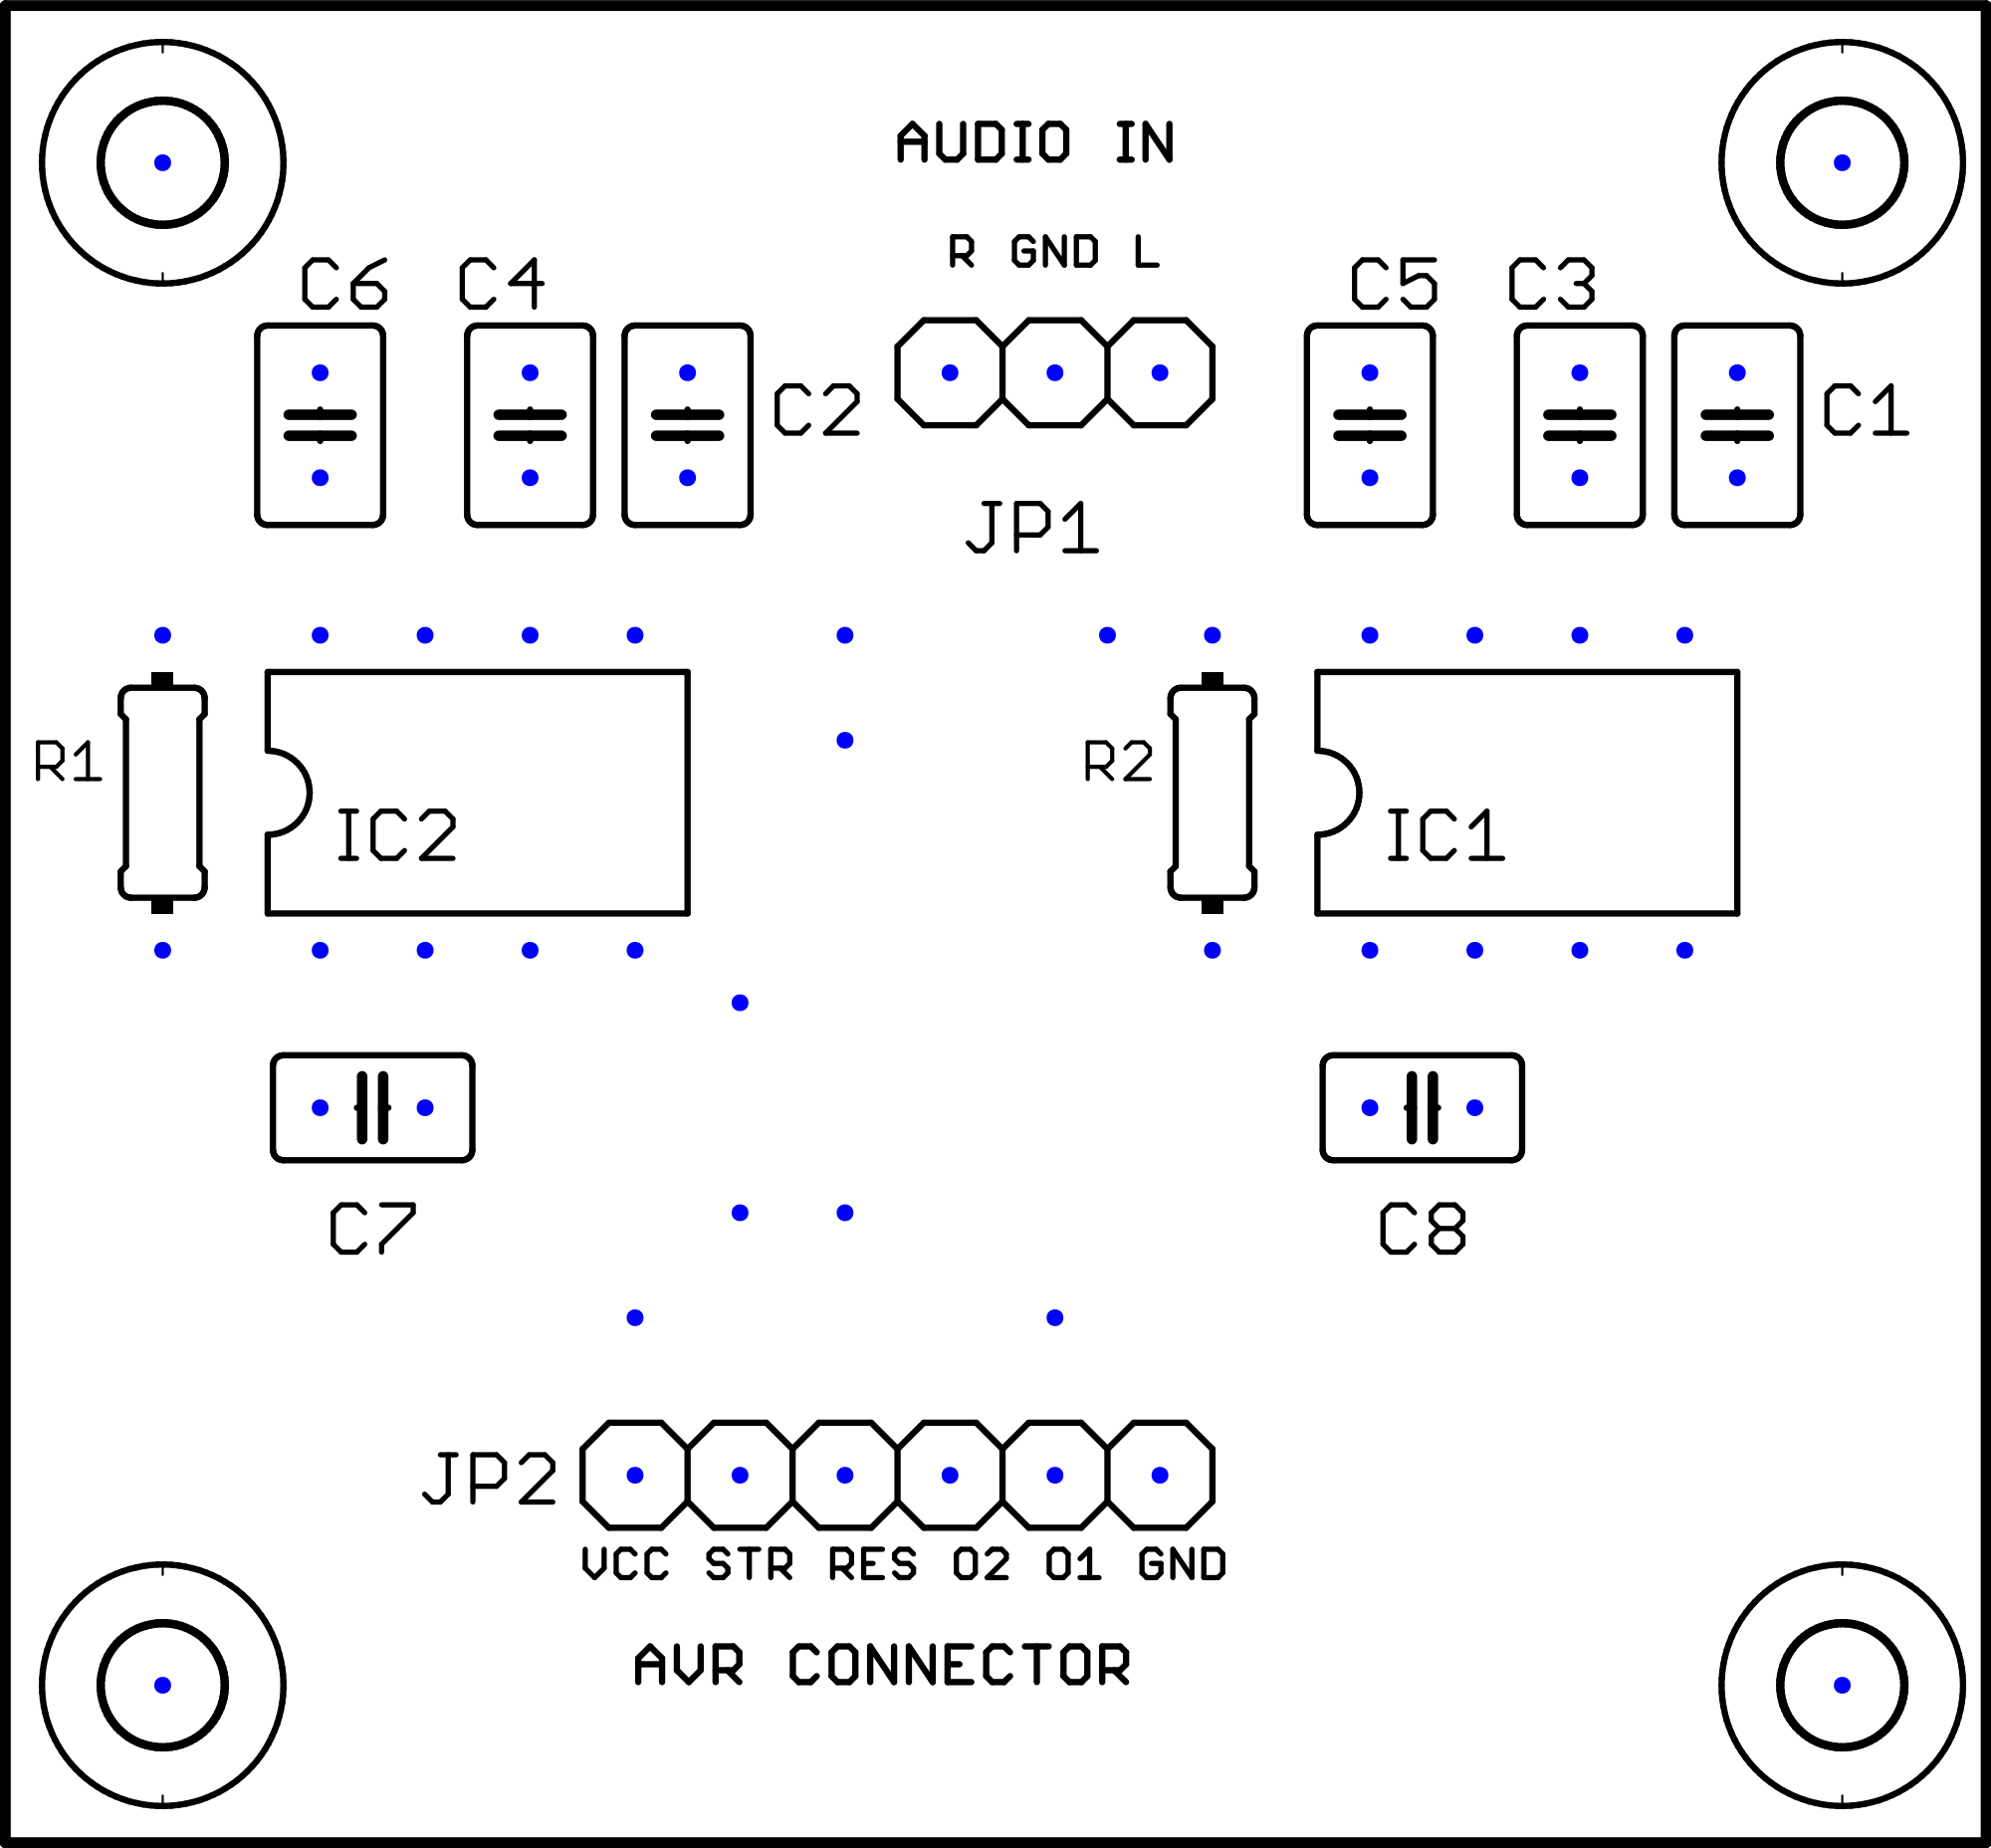
[picture p25: page 1]
