andykarpov/PiRadio-20x4LCD/schematic/build/pdf/msgeq7_v_1_0_pcb_top.pdf

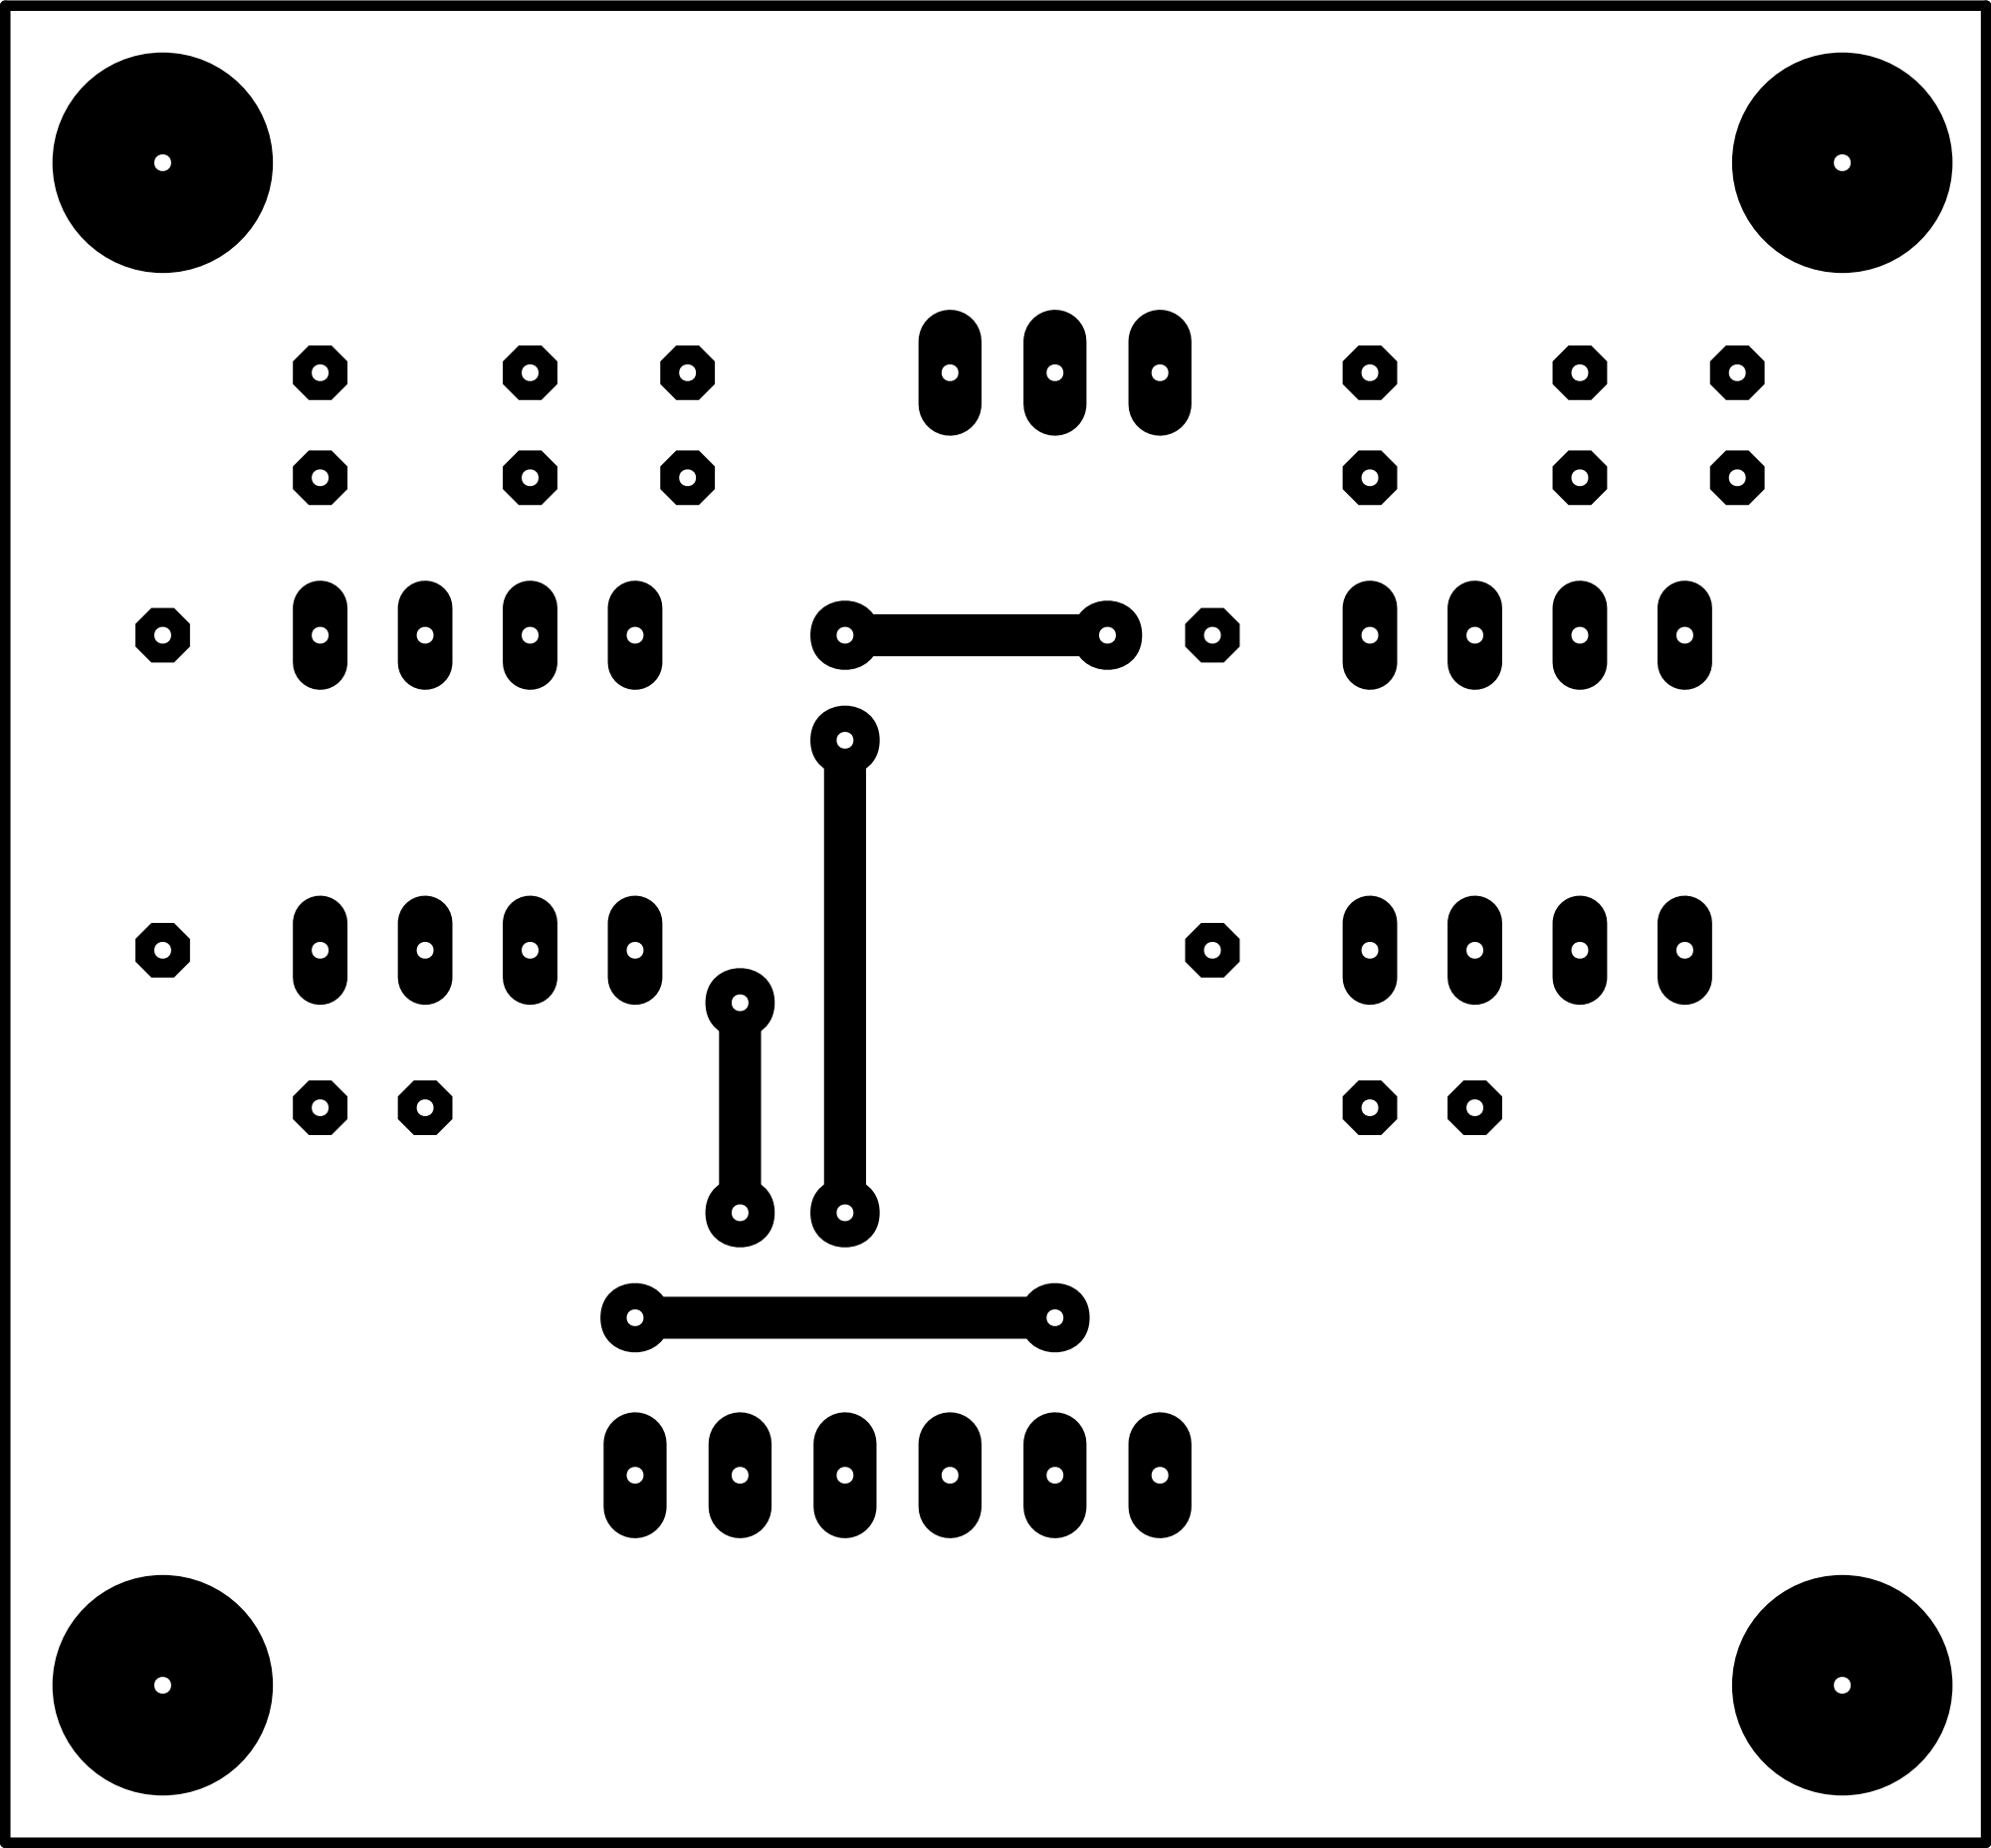
[picture p26: page 1]
