andykarpov/PiRadio-20x4LCD/schematic/build/pdf/power_v_1_0_pcb_bottom.pdf

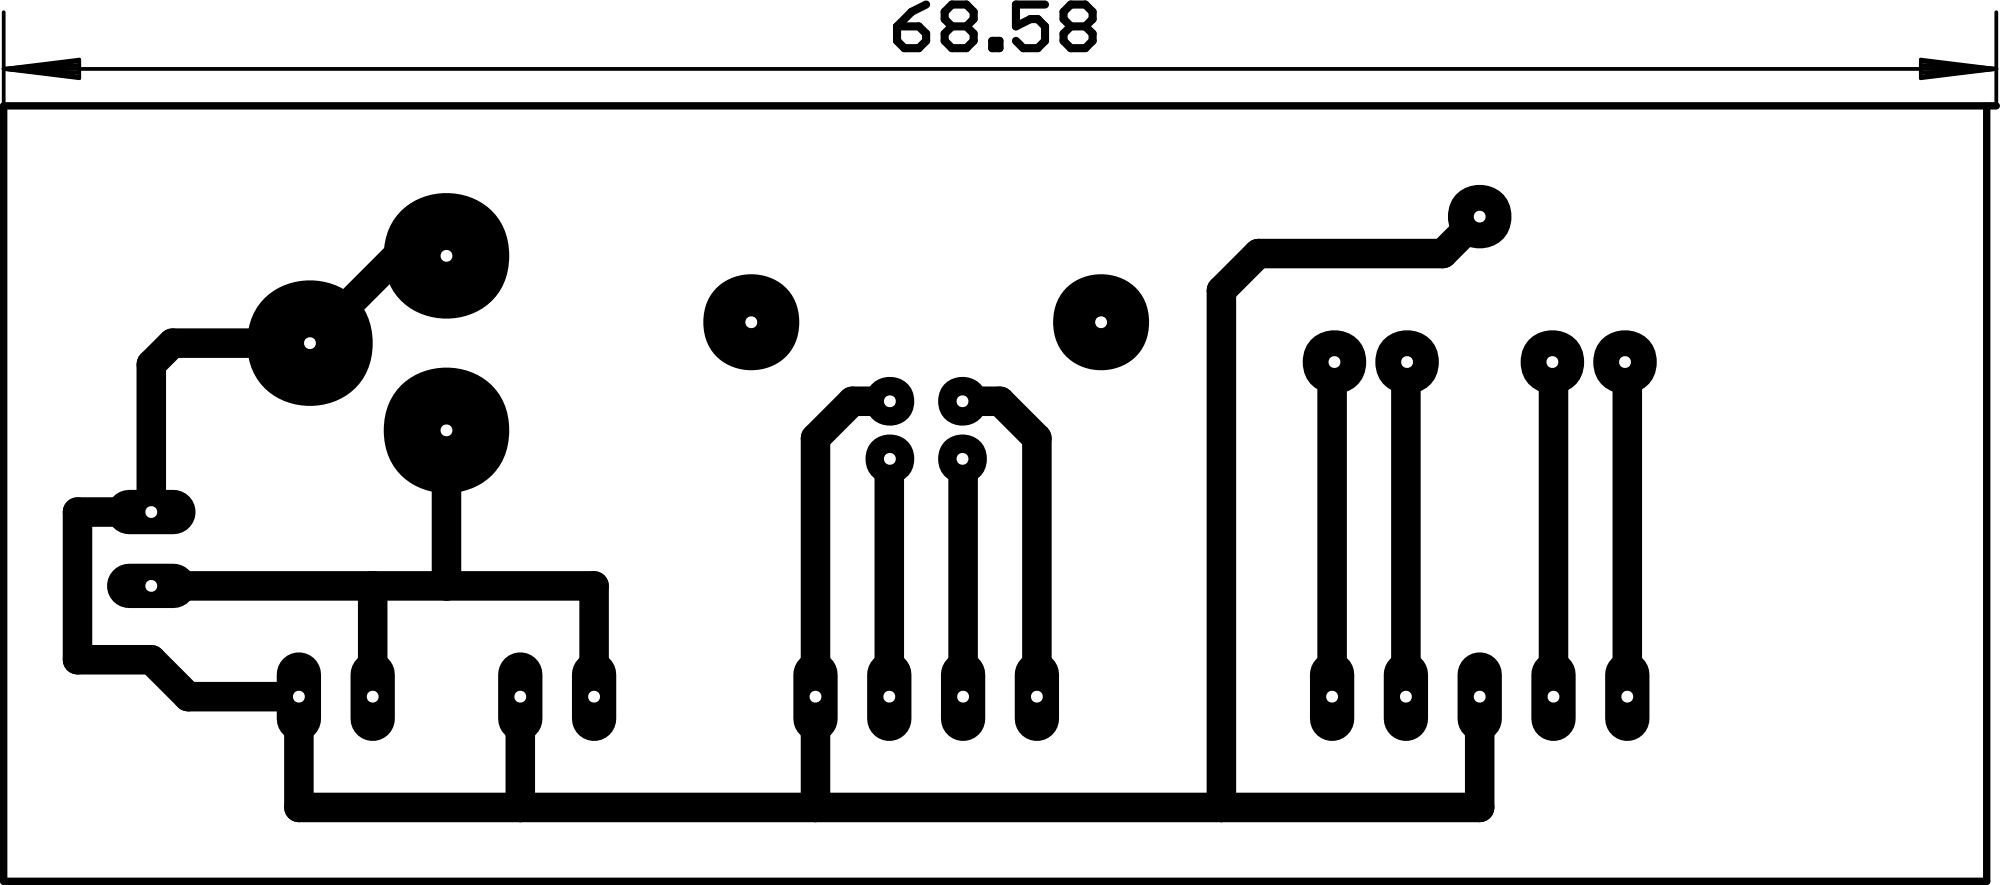
[picture p27: page 1]
