andykarpov/PiRadio-20x4LCD/schematic/build/pdf/power_v_1_0_pcb_cmp.pdf

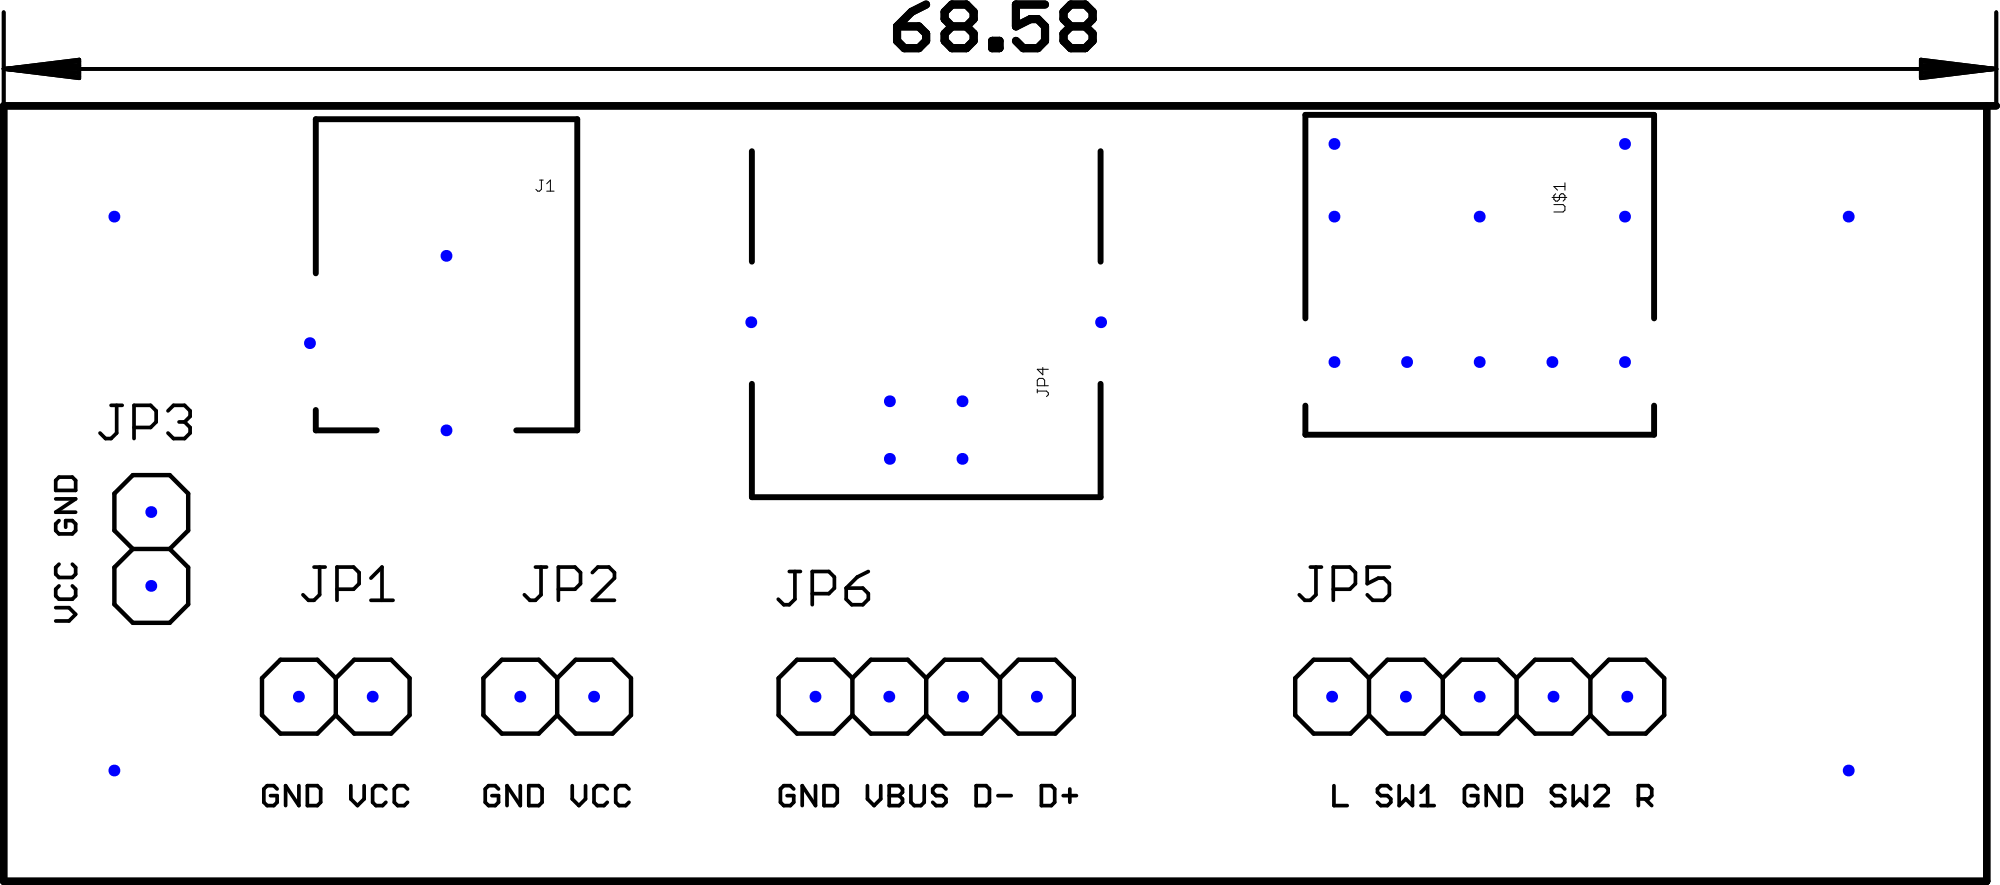
[picture p28: page 1]
