andykarpov/PiRadio-20x4LCD/schematic/build/pdf/power_v_1_0_pcb_top.pdf

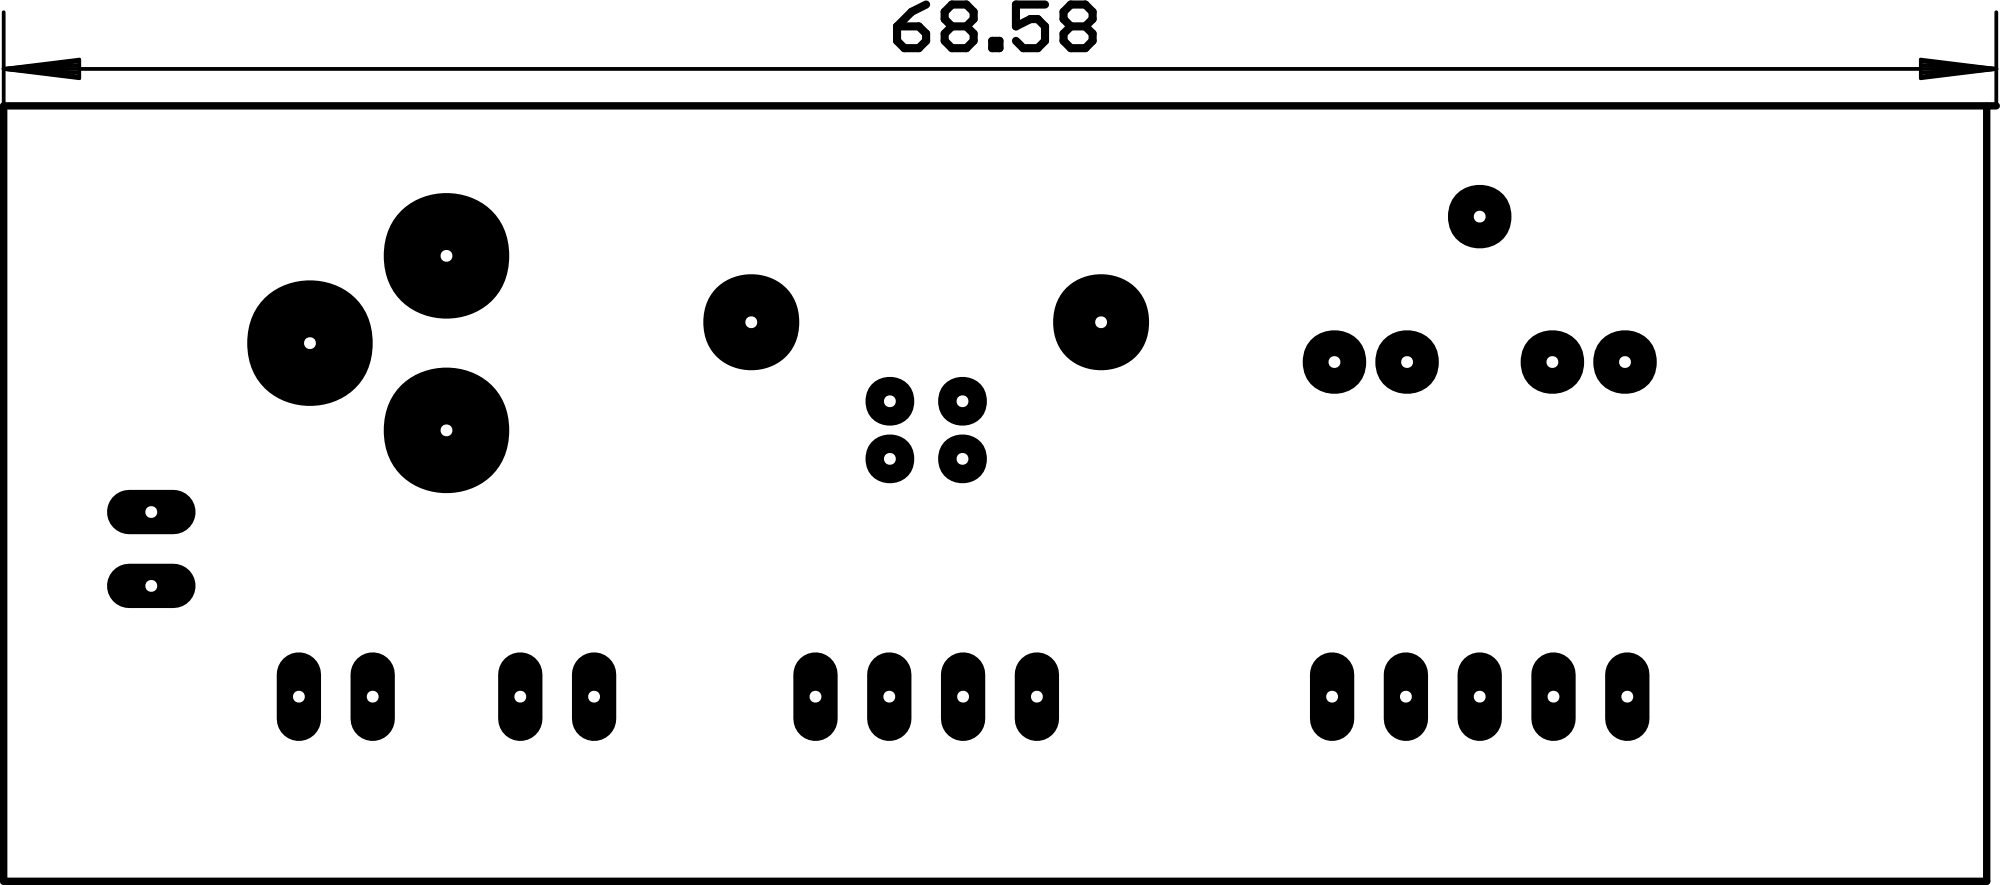
[picture p29: page 1]
