andykarpov/PiRadio-20x4LCD/schematic/build/pdf/pt2322_v_1_0_pcb_bottom.pdf

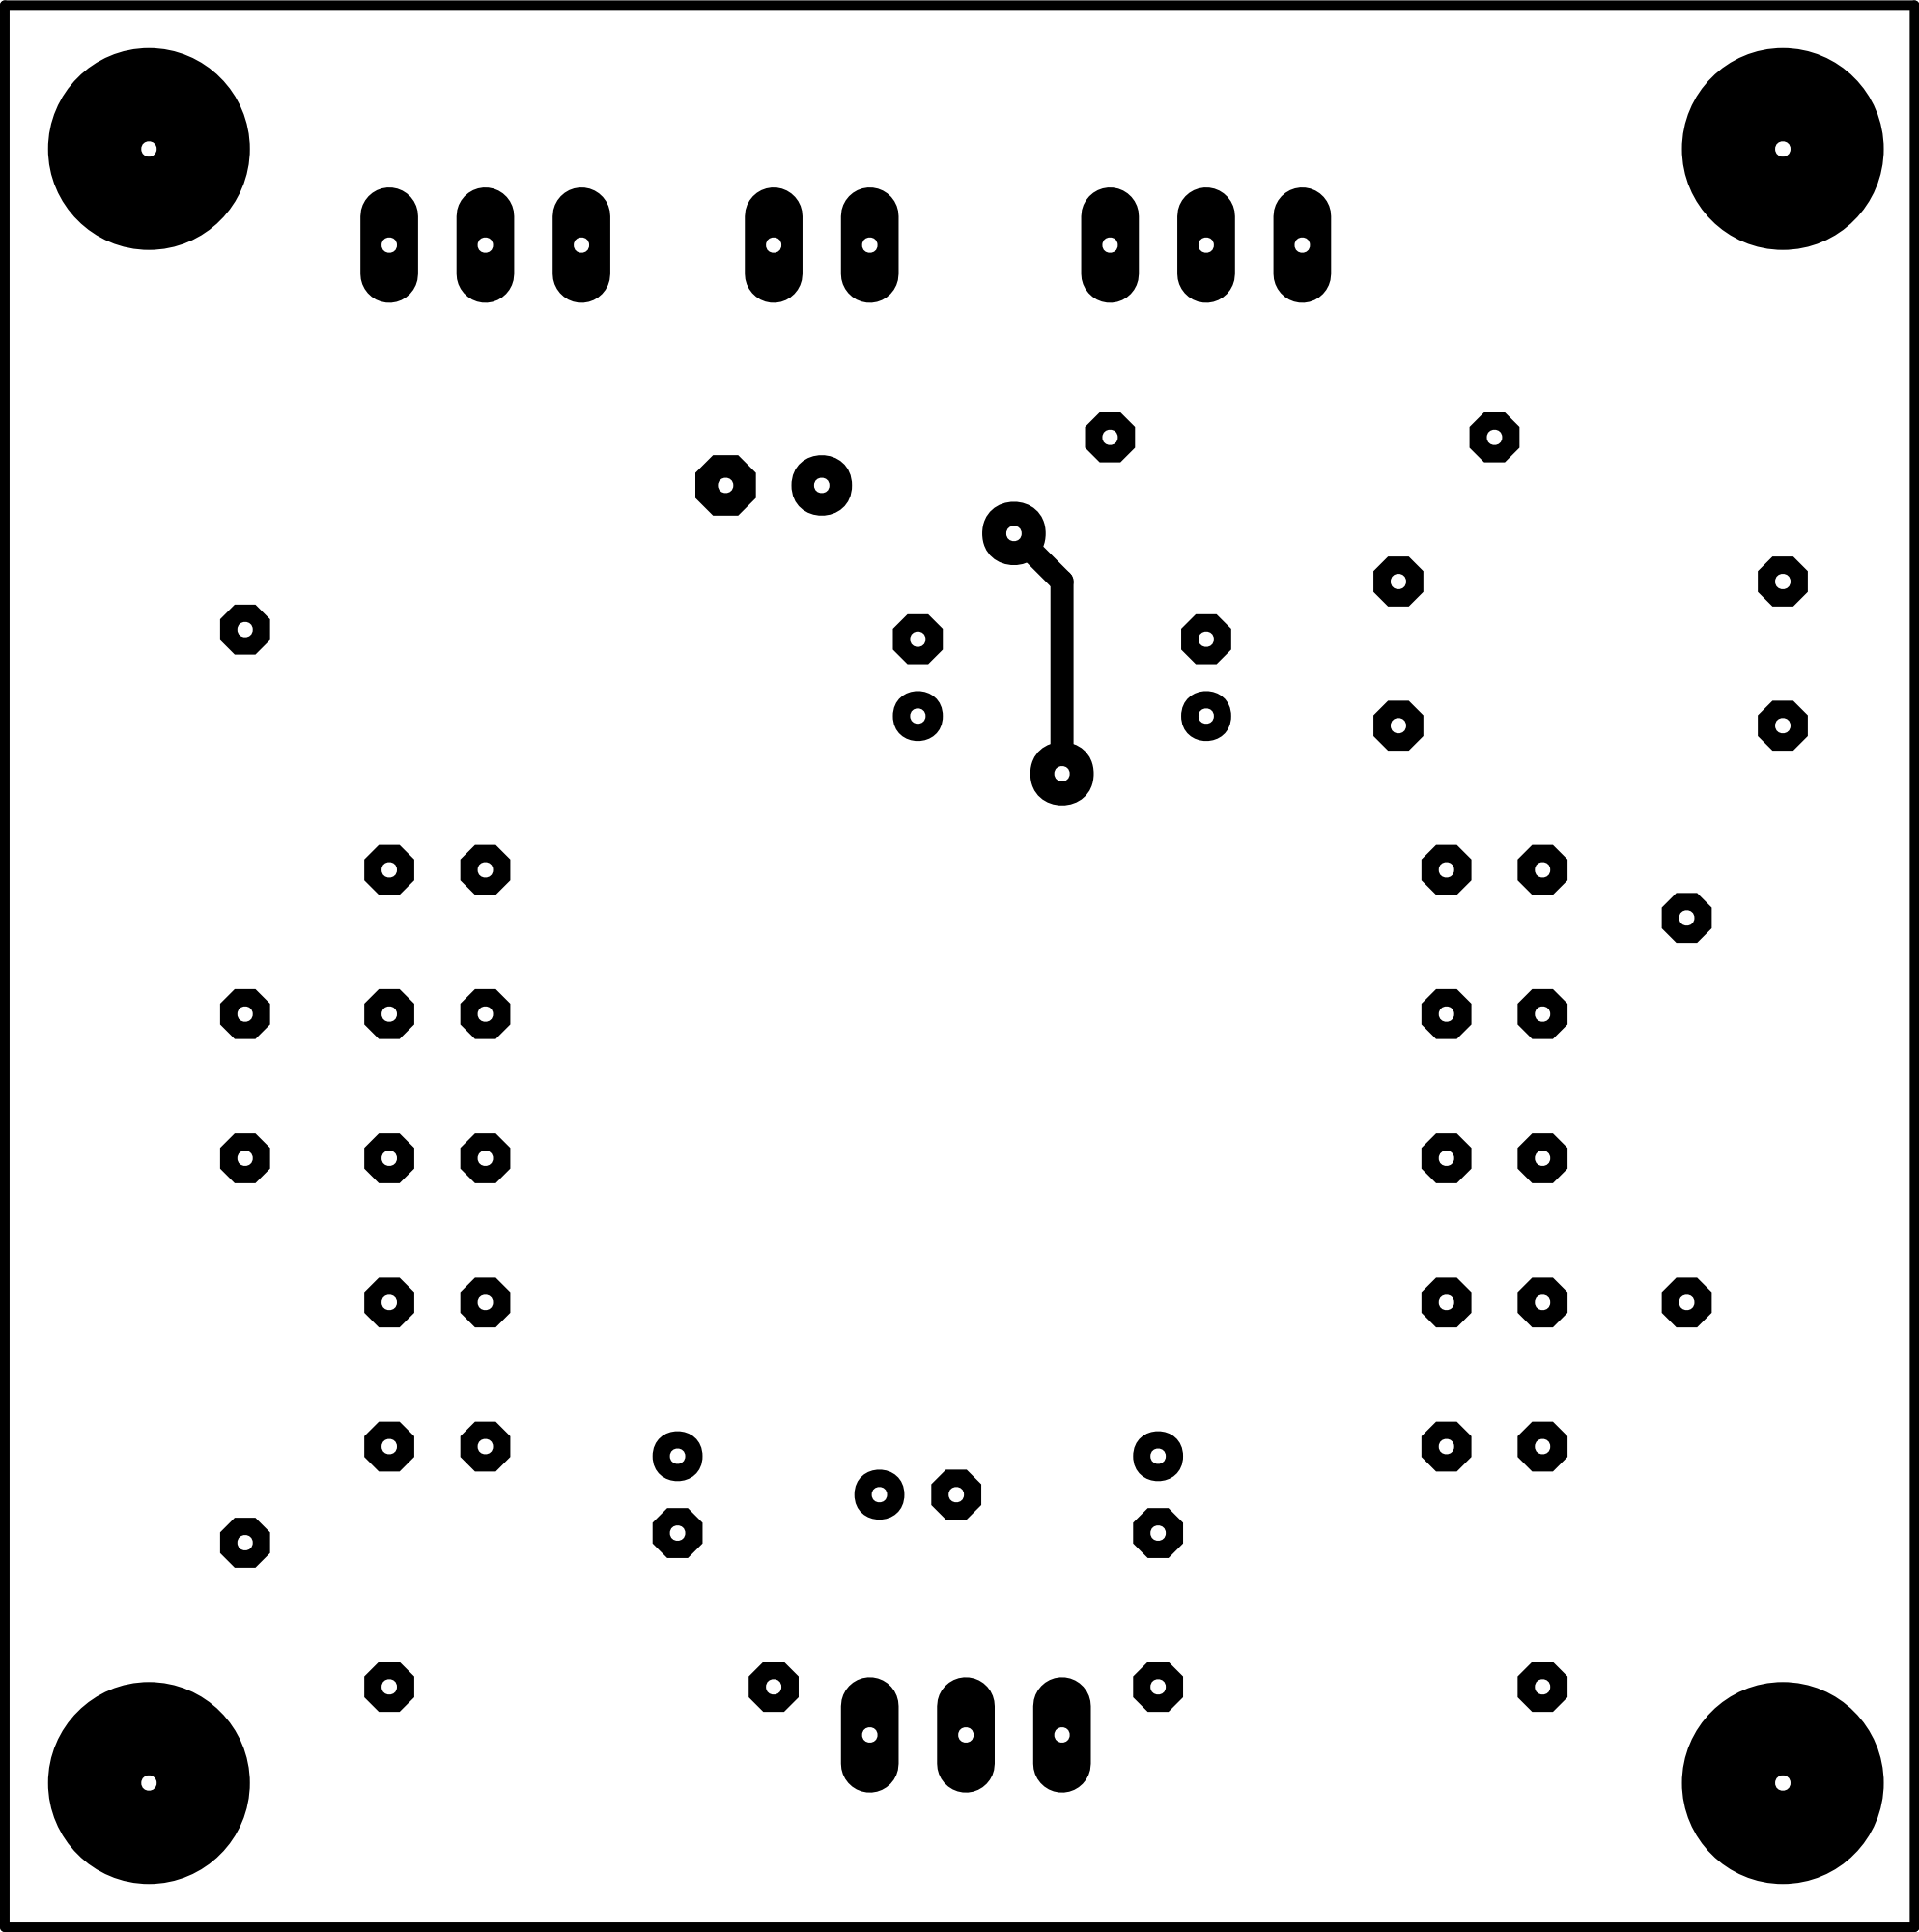
[picture p30: page 1]
