andykarpov/PiRadio-20x4LCD/schematic/build/pdf/pt2322_v_1_0_pcb_cmp.pdf

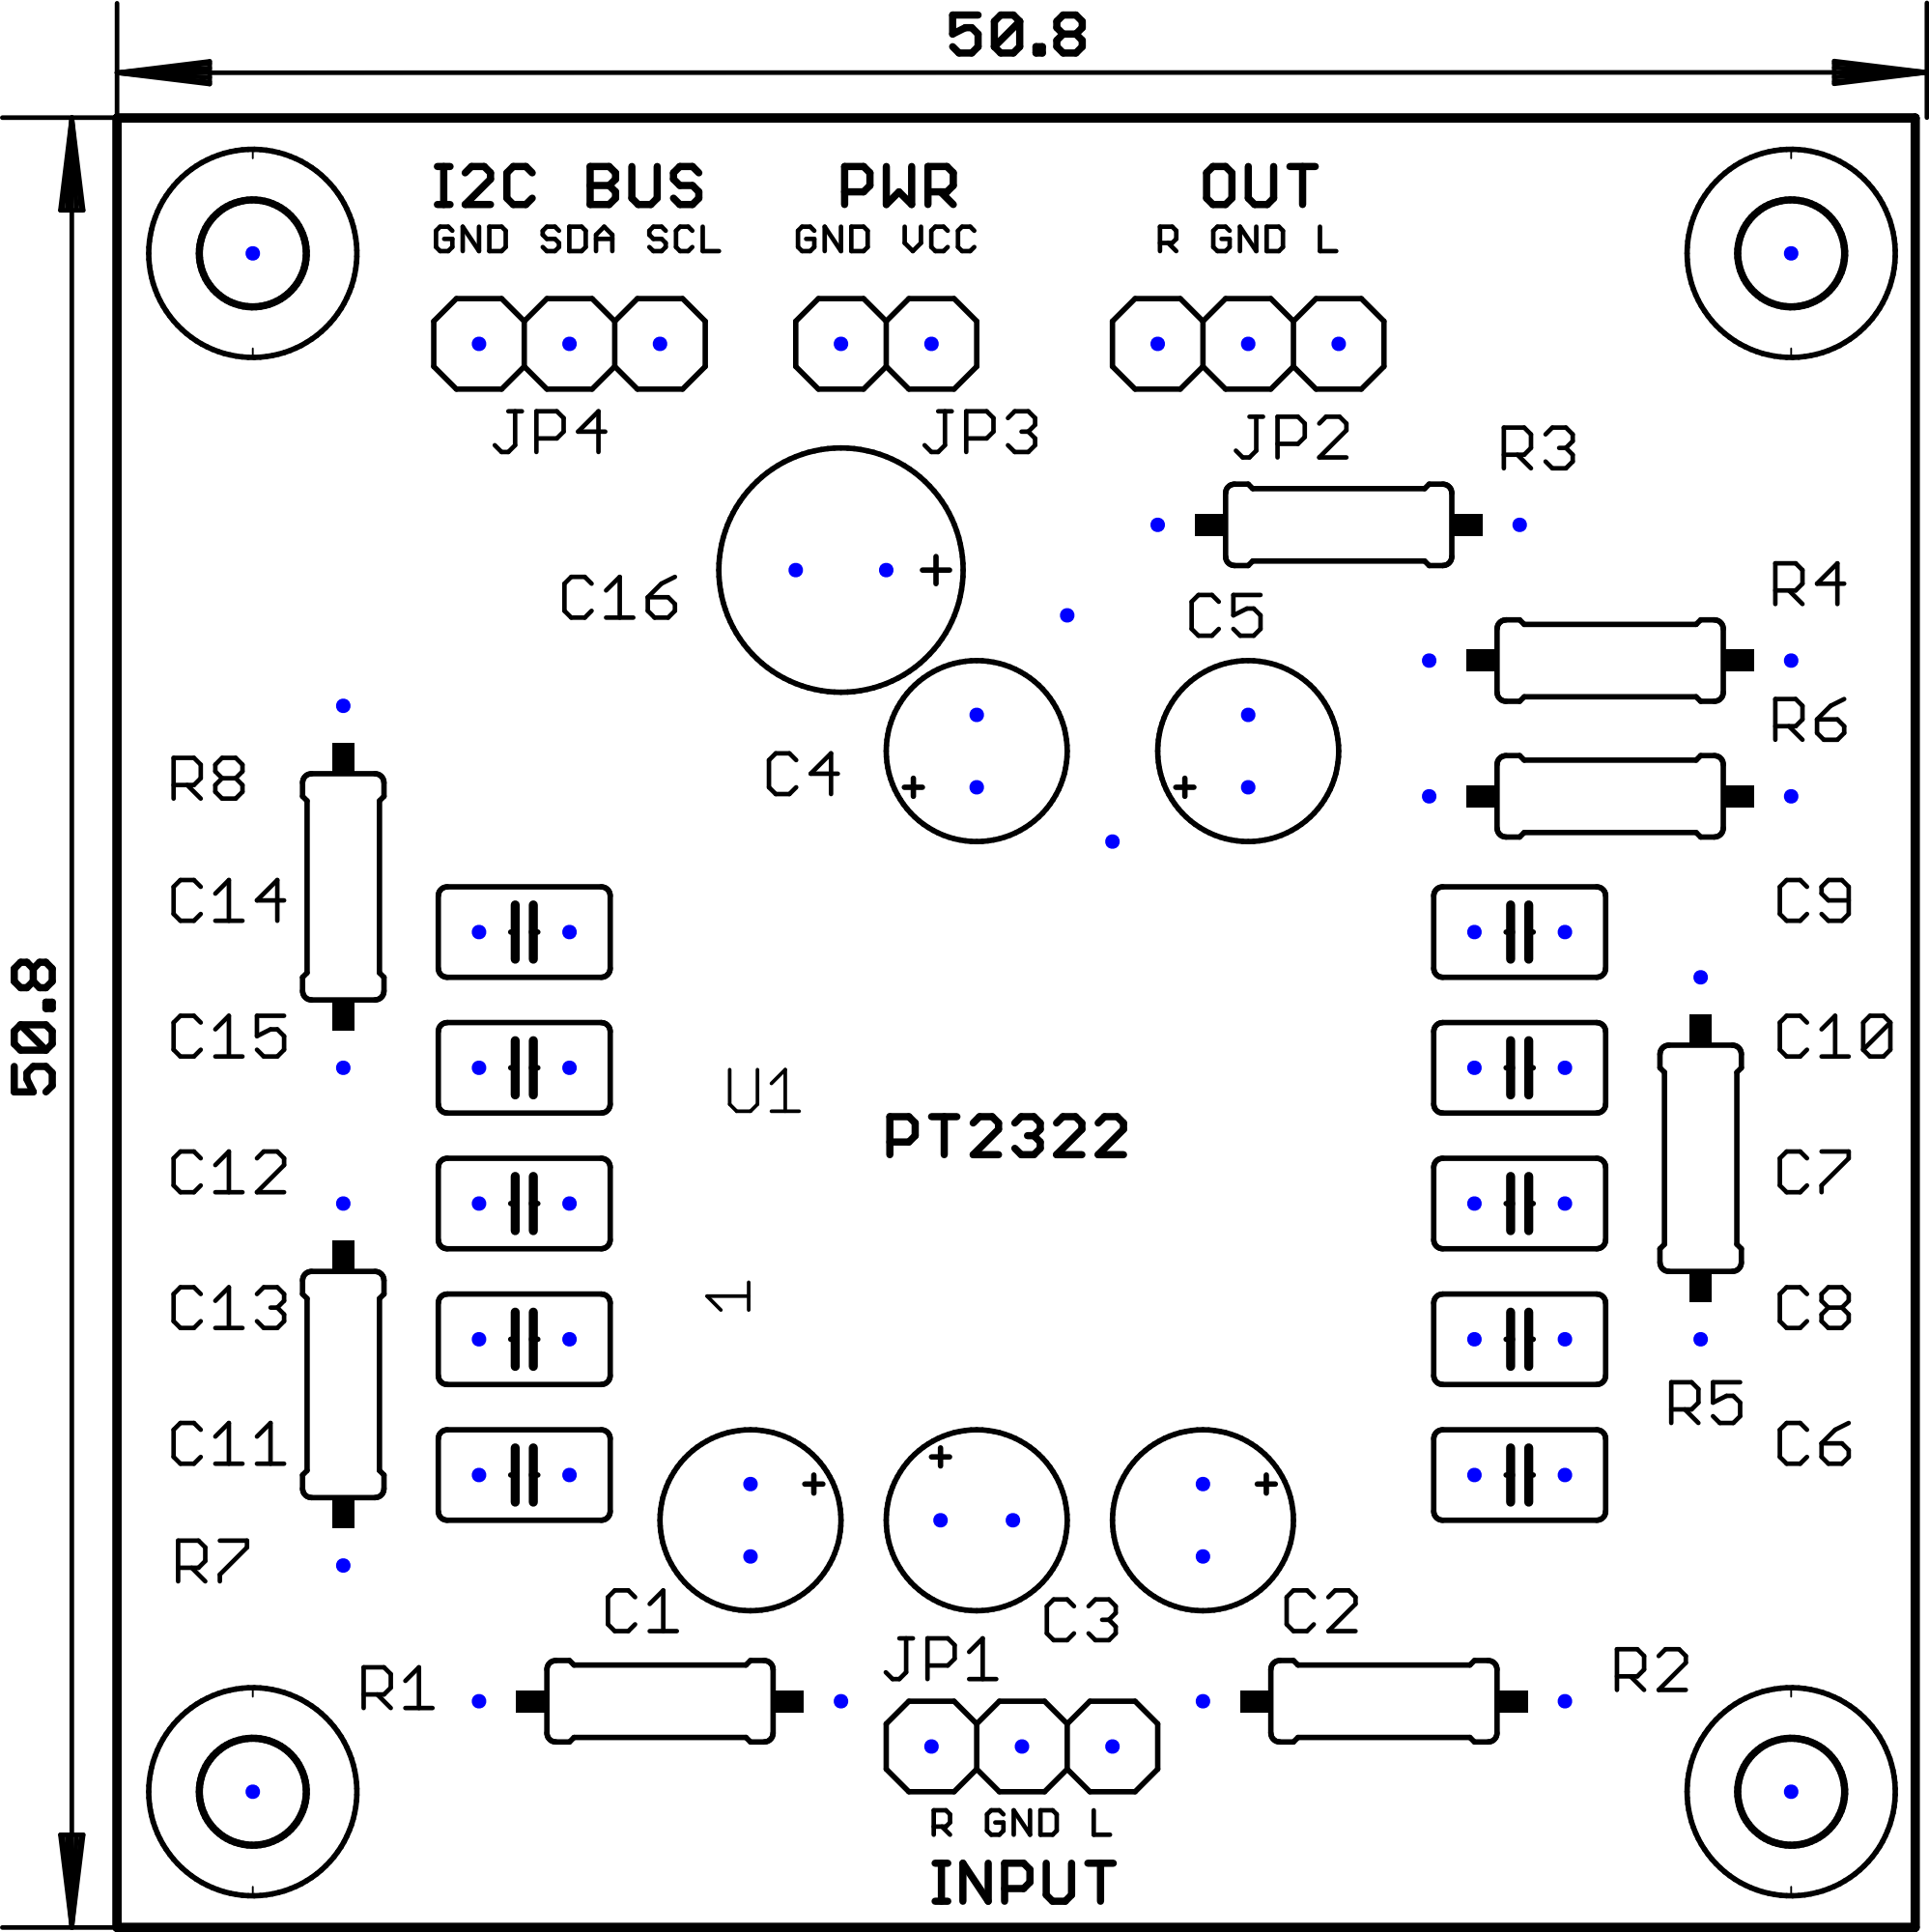
[picture p31: page 1]
