andykarpov/PiRadio-20x4LCD/schematic/build/pdf/pt2322_v_1_0_pcb_top.pdf

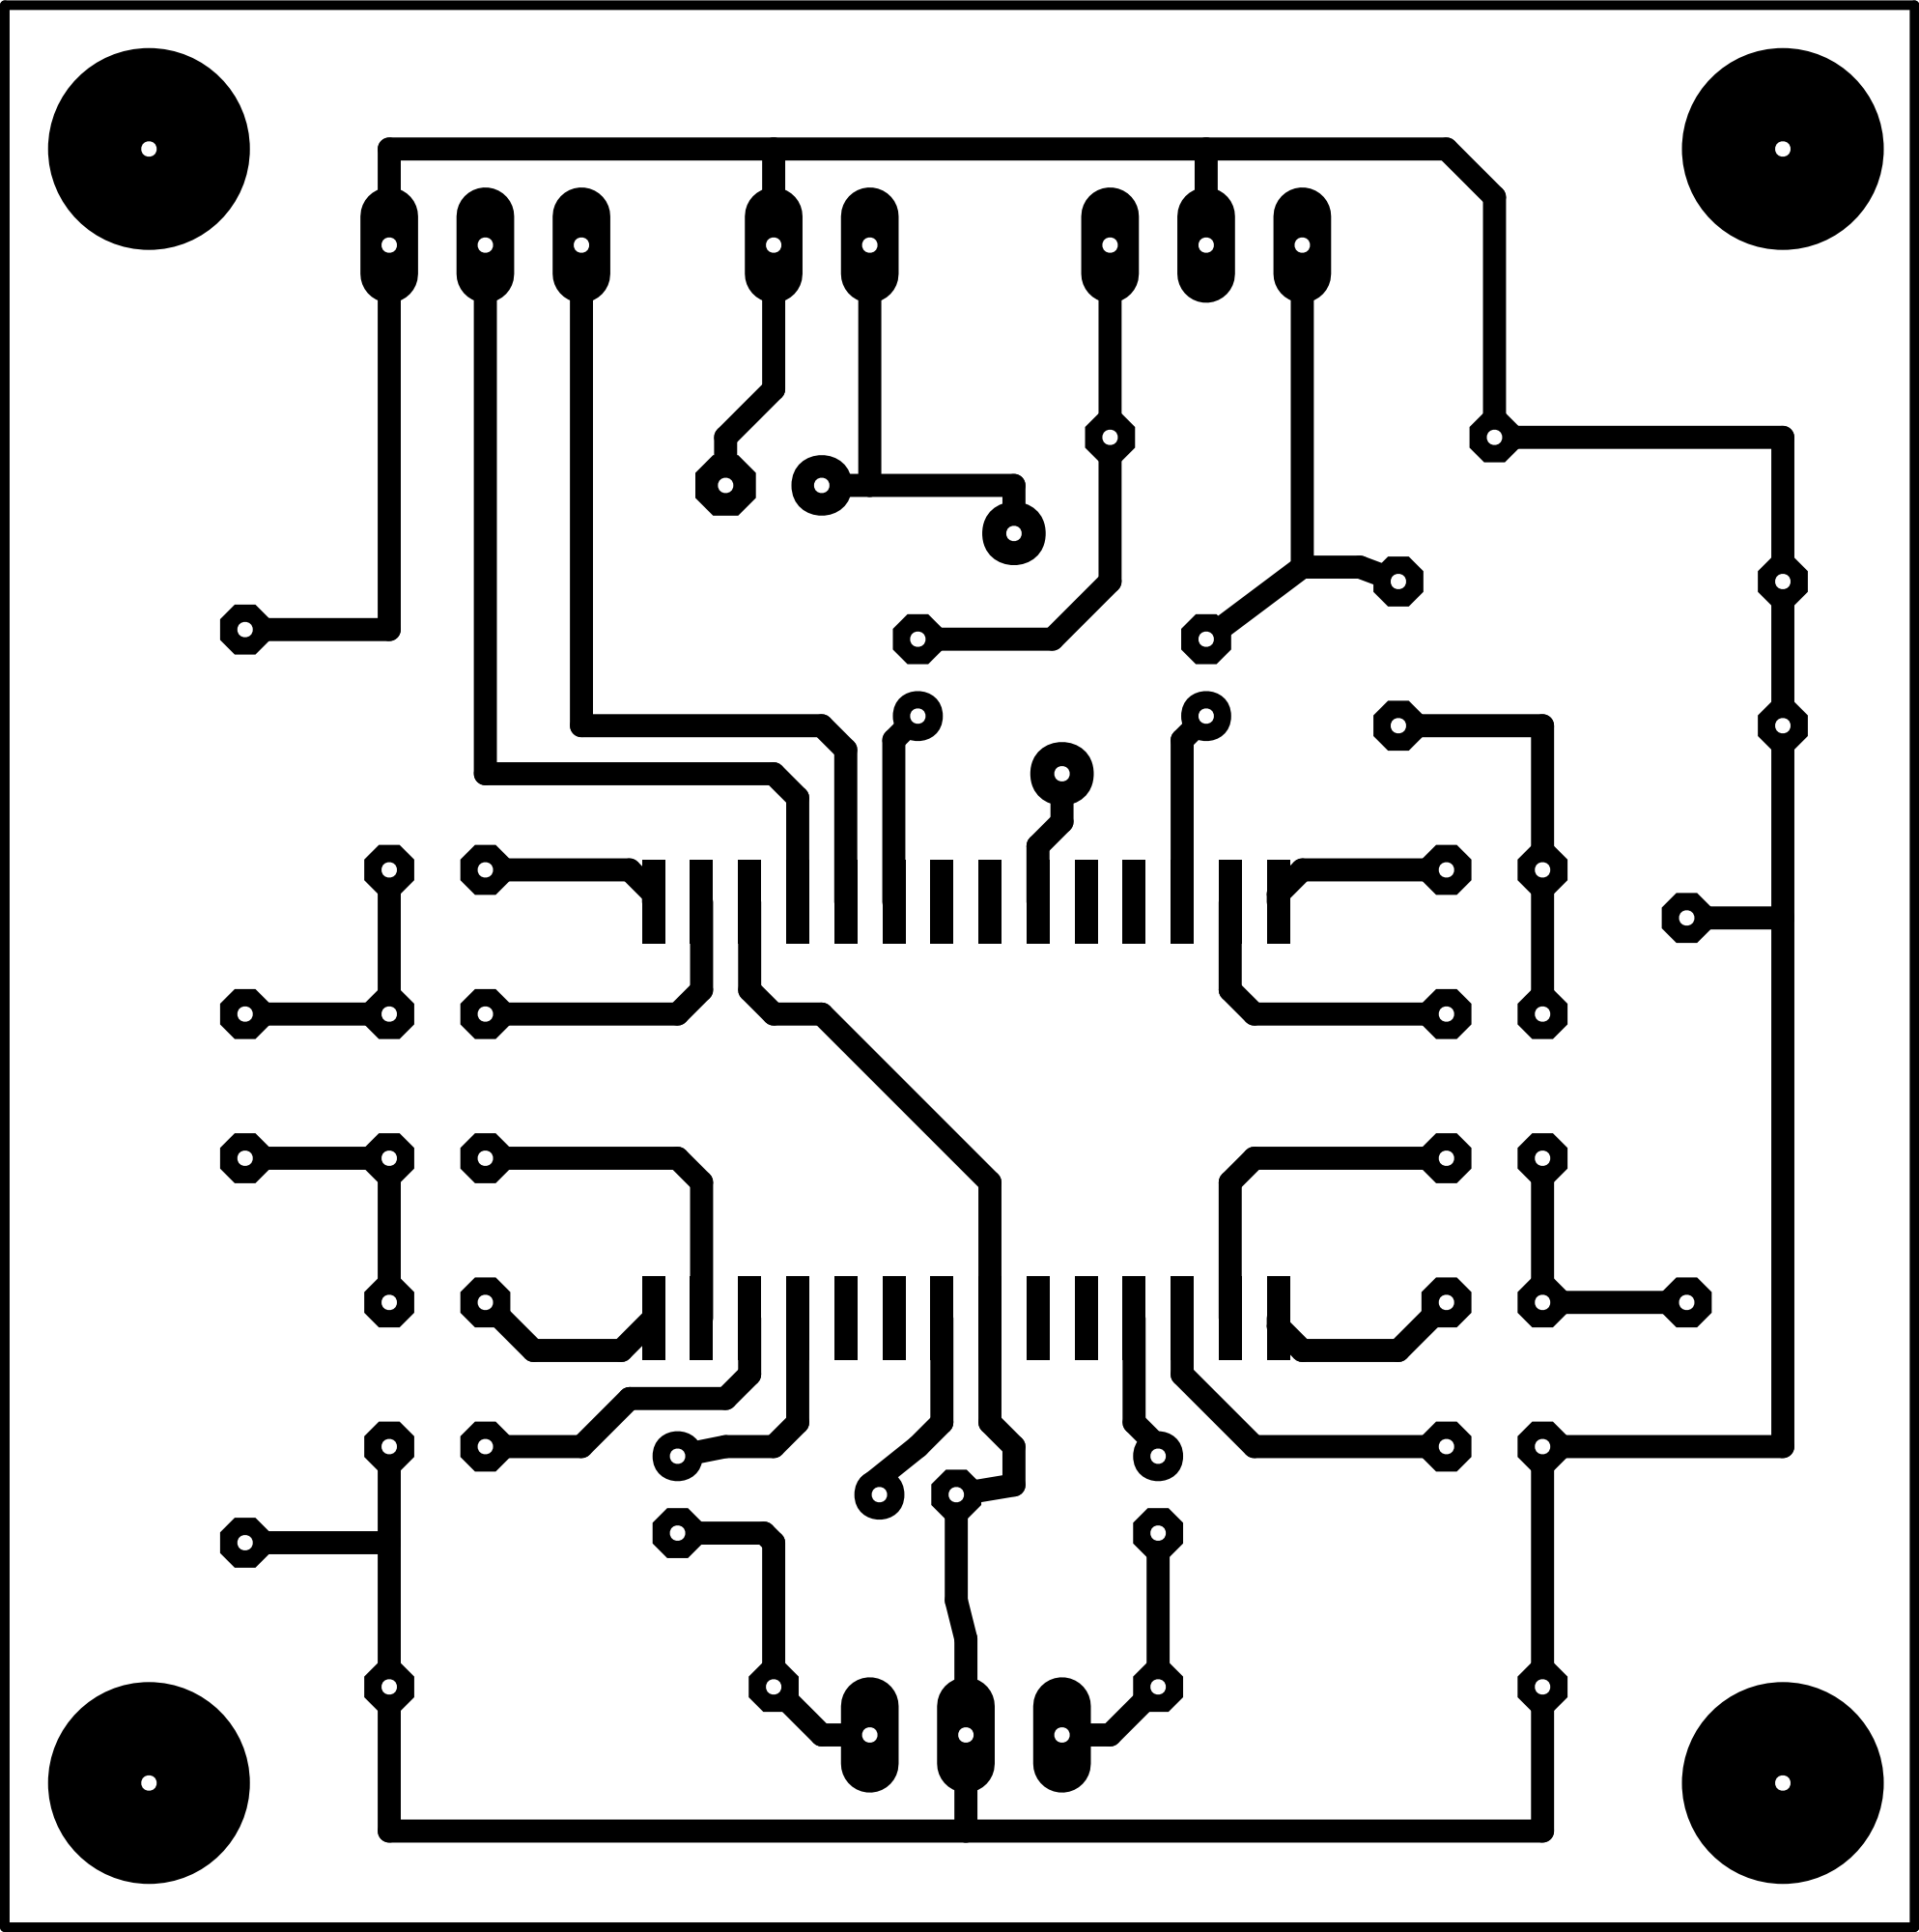
[picture p32: page 1]
