andykarpov/PiRadio-20x4LCD/schematic/build/pdf/test_v_1_0_pcb_bottom.pdf

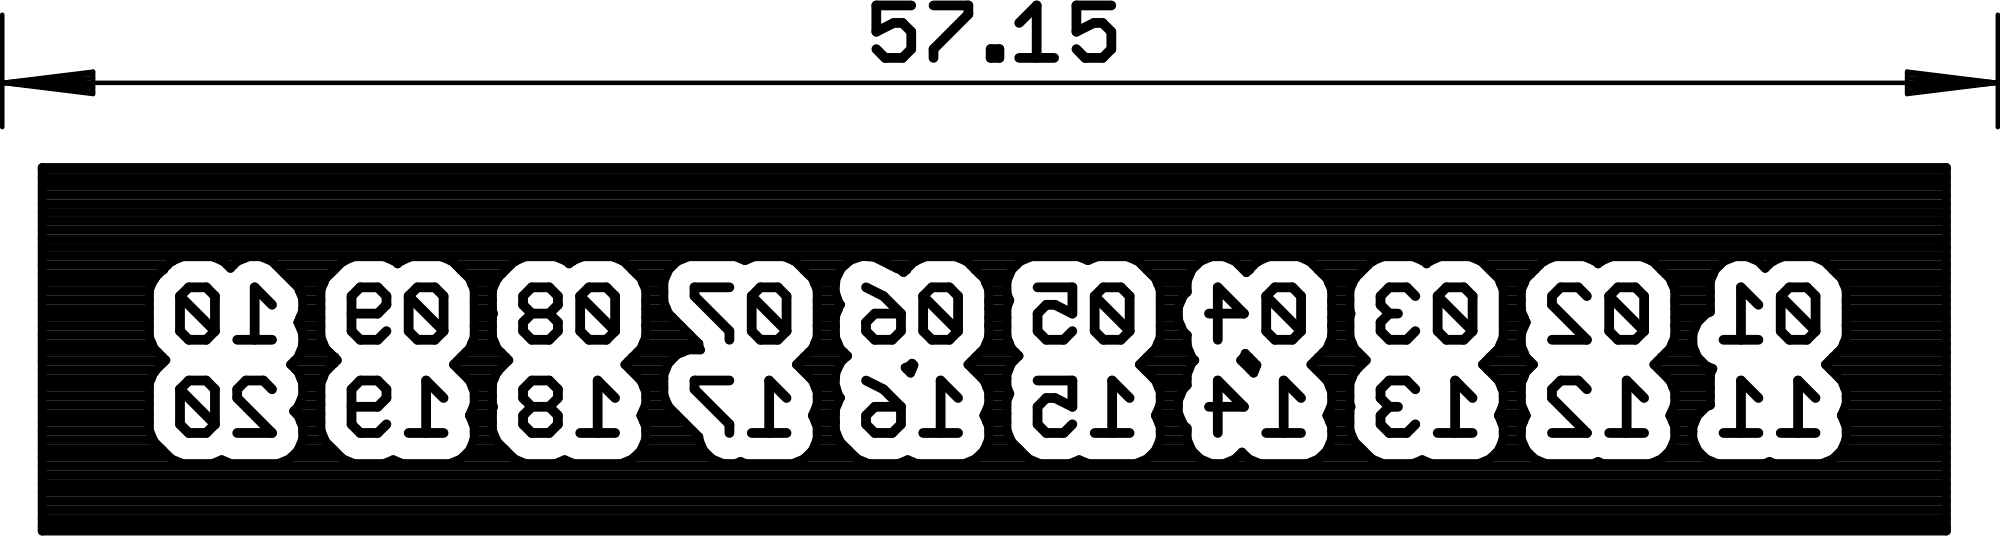
[picture p33: page 1]
