andykarpov/PiRadio-20x4LCD/schematic/build/pdf/volume_v_1_0_pcb_bottom.pdf

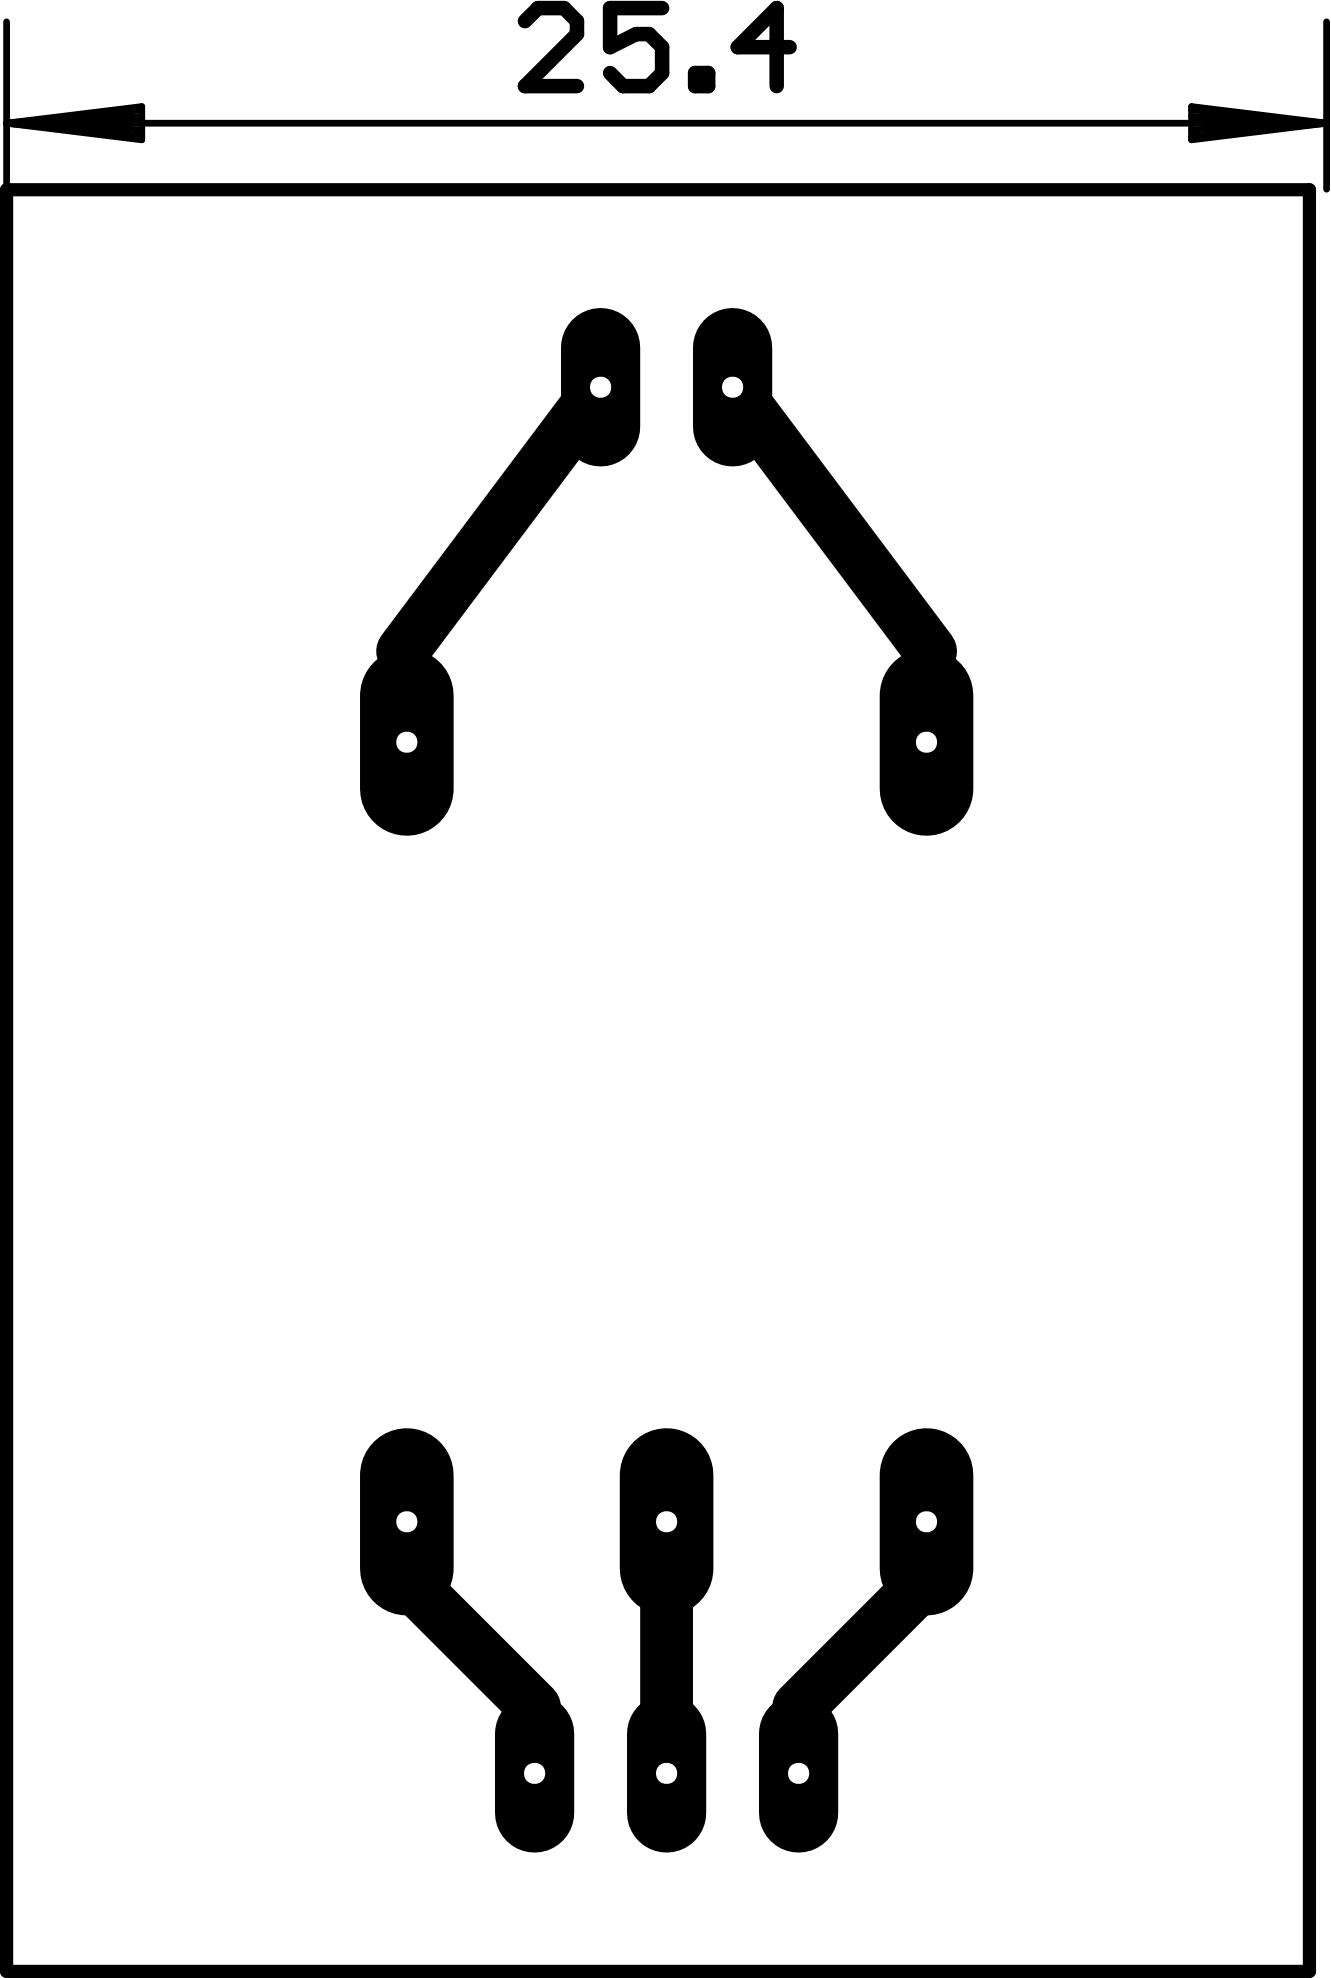
[picture p34: page 1]
