andykarpov/PiRadio-20x4LCD/schematic/build/pdf/volume_v_1_0_pcb_cmp.pdf

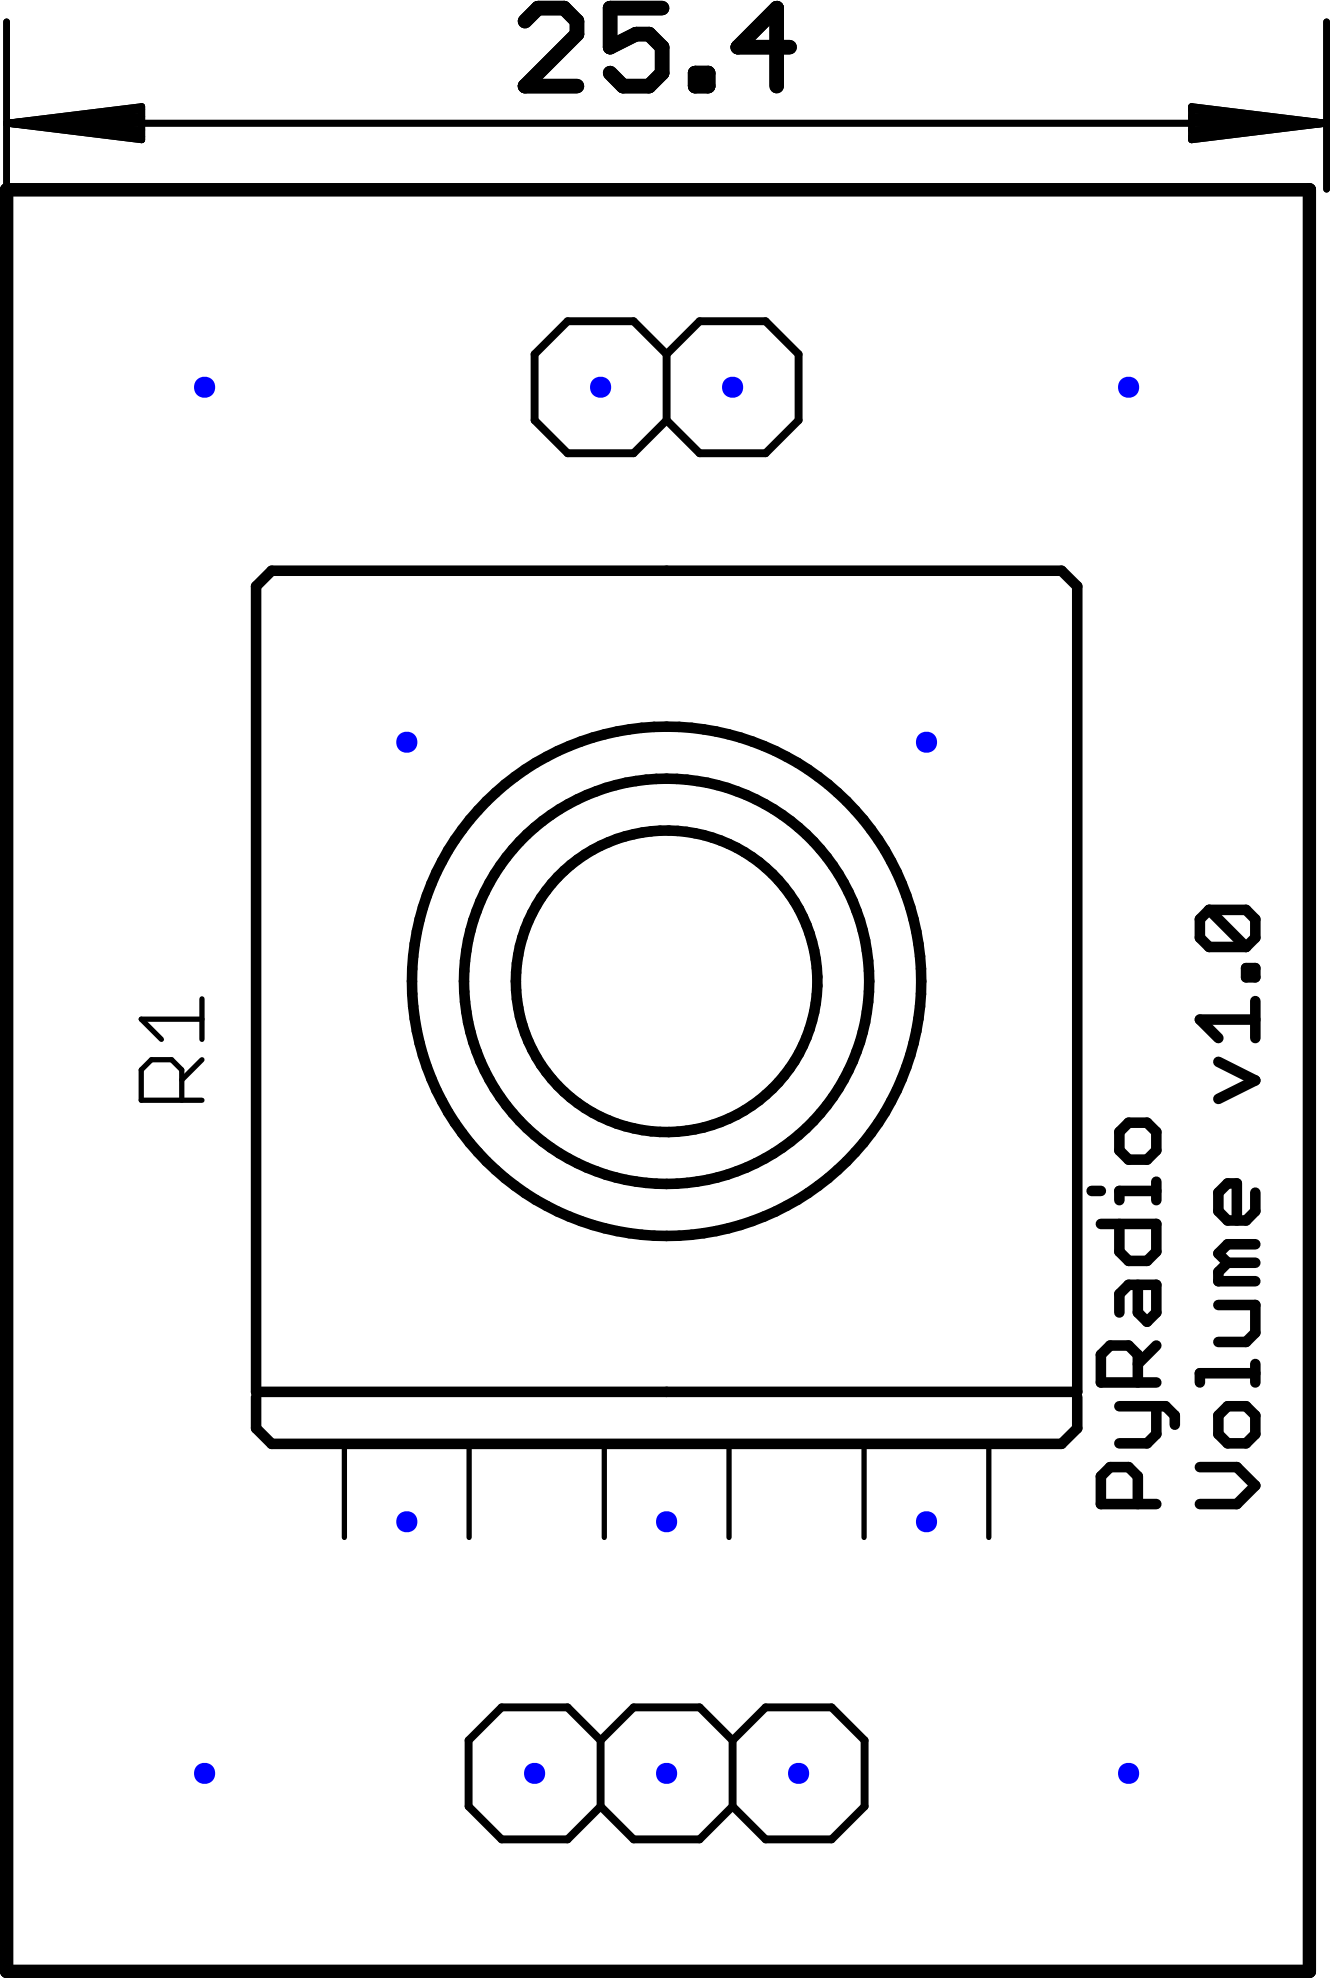
[picture p35: page 1]
